GeorgeHahn/Avalon/cgminer/cgminer.c

/*
 * Copyright 2011-2013 Con Kolivas
 * Copyright 2011-2012 Luke Dashjr
 * Copyright 2010 Jeff Garzik
 *
 * This program is free software; you can redistribute it and/or modify it
 * under the terms of the GNU General Public License as published by the Free
 * Software Foundation; either version 3 of the License, or (at your option)
 * any later version.  See COPYING for more details.
 */

#include "config.h"

#ifdef HAVE_CURSES
#include <curses.h>
#endif

#include <stdio.h>
#include <stdlib.h>
#include <string.h>
#include <stdbool.h>
#include <stdint.h>
#include <unistd.h>
#include <sys/time.h>
#include <time.h>
#include <math.h>
#include <stdarg.h>
#include <assert.h>
#include <signal.h>

#ifdef USE_USBUTILS
#include <semaphore.h>
#endif

#include <sys/stat.h>
#include <sys/types.h>

#ifndef WIN32
#include <sys/resource.h>
#endif
#include <ccan/opt/opt.h>
#include <jansson.h>
#include <curl/curl.h>
#include <libgen.h>
#include <sha2.h>

#include "compat.h"
#include "miner.h"
#include "findnonce.h"
#include "adl.h"
#include "driver-opencl.h"
#include "bench_block.h"
#include "scrypt.h"

#ifdef USE_AVALON
#include "driver-avalon.h"
#endif

#if defined(unix) || defined(__APPLE__)
	#include <errno.h>
	#include <fcntl.h>
	#include <sys/wait.h>
#endif

#if defined(USE_BITFORCE) || defined(USE_ICARUS) || defined(USE_AVALON) || defined(USE_MODMINER)
#	define USE_FPGA
#elif defined(USE_ZTEX)
#	define USE_FPGA
#endif

struct strategies strategies[] = {
	{ "Failover" },
	{ "Round Robin" },
	{ "Rotate" },
	{ "Load Balance" },
	{ "Balance" },
};

static char packagename[256];

bool opt_protocol;
static bool opt_benchmark;
bool have_longpoll;
bool want_per_device_stats;
bool use_syslog;
bool opt_quiet;
bool opt_realquiet;
bool opt_loginput;
bool opt_compact;
const int opt_cutofftemp = 95;
int opt_log_interval = 5;
int opt_queue = 1;
int opt_scantime = -1;
int opt_expiry = 120;
static const bool opt_time = true;
unsigned long long global_hashrate;

#if defined(HAVE_OPENCL) || defined(USE_USBUTILS)
int nDevs;
#endif
#ifdef HAVE_OPENCL
int opt_dynamic_interval = 7;
int opt_g_threads = -1;
int gpu_threads;
#ifdef USE_SCRYPT
bool opt_scrypt;
#endif
#endif
bool opt_restart = true;
static bool opt_nogpu;

struct list_head scan_devices;
static bool devices_enabled[MAX_DEVICES];
static int opt_devs_enabled;
static bool opt_display_devs;
static bool opt_removedisabled;
int total_devices;
int zombie_devs;
static int most_devices;
struct cgpu_info **devices;
bool have_opencl;
int mining_threads;
int num_processors;
#ifdef HAVE_CURSES
bool use_curses = true;
#else
bool use_curses;
#endif
static bool opt_submit_stale = true;
static int opt_shares;
bool opt_fail_only;
static bool opt_fix_protocol;
static bool opt_lowmem;
bool opt_autofan;
bool opt_autoengine;
bool opt_noadl;
char *opt_api_allow = NULL;
char *opt_api_groups;
char *opt_api_description = PACKAGE_STRING;
int opt_api_port = 4028;
bool opt_api_listen;
bool opt_api_network;
bool opt_delaynet;
bool opt_disable_pool;
char *opt_icarus_options = NULL;
char *opt_icarus_timing = NULL;
char *opt_klondike_options = NULL;
bool opt_worktime;
#ifdef USE_AVALON
char *opt_avalon_options = NULL;
#endif
#ifdef USE_USBUTILS
char *opt_usb_select = NULL;
int opt_usbdump = -1;
bool opt_usb_list_all;
cgsem_t usb_resource_sem;
#endif

char *opt_kernel_path;
char *cgminer_path;

#if defined(USE_BITFORCE)
bool opt_bfl_noncerange;
#endif
#define QUIET	(opt_quiet || opt_realquiet)

struct thr_info *control_thr;
struct thr_info **mining_thr;
static int gwsched_thr_id;
static int stage_thr_id;
static int watchpool_thr_id;
static int watchdog_thr_id;
#ifdef HAVE_CURSES
static int input_thr_id;
#endif
int gpur_thr_id;
static int api_thr_id;
#ifdef USE_USBUTILS
static int usbres_thr_id;
static int hotplug_thr_id;
#endif
static int total_control_threads;
bool hotplug_mode;
static int new_devices;
static int new_threads;
int hotplug_time = 5;

#ifdef USE_USBUTILS
pthread_mutex_t cgusb_lock;
pthread_mutex_t cgusbres_lock;
cglock_t cgusb_fd_lock;
#endif

pthread_mutex_t hash_lock;
static pthread_mutex_t *stgd_lock;
pthread_mutex_t console_lock;
cglock_t ch_lock;
static pthread_rwlock_t blk_lock;
static pthread_mutex_t sshare_lock;

pthread_rwlock_t netacc_lock;
pthread_rwlock_t mining_thr_lock;
pthread_rwlock_t devices_lock;

static pthread_mutex_t lp_lock;
static pthread_cond_t lp_cond;

pthread_mutex_t restart_lock;
pthread_cond_t restart_cond;

pthread_cond_t gws_cond;

double total_mhashes_done;
static struct timeval total_tv_start, total_tv_end;

cglock_t control_lock;
pthread_mutex_t stats_lock;

int hw_errors;
int total_accepted, total_rejected, total_diff1;
int total_getworks, total_stale, total_discarded;
double total_diff_accepted, total_diff_rejected, total_diff_stale;
static int staged_rollable;
unsigned int new_blocks;
static unsigned int work_block;
unsigned int found_blocks;

unsigned int local_work;
unsigned int total_go, total_ro;

struct pool **pools;
static struct pool *currentpool = NULL;

int total_pools, enabled_pools;
enum pool_strategy pool_strategy = POOL_FAILOVER;
int opt_rotate_period;
static int total_urls, total_users, total_passes, total_userpasses;

static
#ifndef HAVE_CURSES
const
#endif
bool curses_active;

static char current_block[40];

/* Protected by ch_lock */
static char *current_hash;
char *current_fullhash;

static char datestamp[40];
static char blocktime[32];
struct timeval block_timeval;
static char best_share[8] = "0";
double current_diff = 0xFFFFFFFFFFFFFFFFULL;
static char block_diff[8];
uint64_t best_diff = 0;

struct block {
	char hash[40];
	UT_hash_handle hh;
	int block_no;
};

static struct block *blocks = NULL;


int swork_id;

/* For creating a hash database of stratum shares submitted that have not had
 * a response yet */
struct stratum_share {
	UT_hash_handle hh;
	bool block;
	struct work *work;
	int id;
	time_t sshare_time;
};

static struct stratum_share *stratum_shares = NULL;

char *opt_socks_proxy = NULL;

static const char def_conf[] = "cgminer.conf";
static char *default_config;
static bool config_loaded;
static int include_count;
#define JSON_INCLUDE_CONF "include"
#define JSON_LOAD_ERROR "JSON decode of file '%s' failed\n %s"
#define JSON_LOAD_ERROR_LEN strlen(JSON_LOAD_ERROR)
#define JSON_MAX_DEPTH 10
#define JSON_MAX_DEPTH_ERR "Too many levels of JSON includes (limit 10) or a loop"

#if defined(unix) || defined(__APPLE__)
	static char *opt_stderr_cmd = NULL;
	static int forkpid;
#endif // defined(unix)

struct sigaction termhandler, inthandler;

struct thread_q *getq;

static int total_work;
struct work *staged_work = NULL;

struct schedtime {
	bool enable;
	struct tm tm;
};

struct schedtime schedstart;
struct schedtime schedstop;
bool sched_paused;

static bool time_before(struct tm *tm1, struct tm *tm2)
{
	if (tm1->tm_hour < tm2->tm_hour)
		return true;
	if (tm1->tm_hour == tm2->tm_hour && tm1->tm_min < tm2->tm_min)
		return true;
	return false;
}

static bool should_run(void)
{
	struct timeval tv;
	struct tm *tm;

	if (!schedstart.enable && !schedstop.enable)
		return true;

	cgtime(&tv);
	const time_t tmp_time = tv.tv_sec;
	tm = localtime(&tmp_time);
	if (schedstart.enable) {
		if (!schedstop.enable) {
			if (time_before(tm, &schedstart.tm))
				return false;

			/* This is a once off event with no stop time set */
			schedstart.enable = false;
			return true;
		}
		if (time_before(&schedstart.tm, &schedstop.tm)) {
			if (time_before(tm, &schedstop.tm) && !time_before(tm, &schedstart.tm))
				return true;
			return false;
		} /* Times are reversed */
		if (time_before(tm, &schedstart.tm)) {
			if (time_before(tm, &schedstop.tm))
				return true;
			return false;
		}
		return true;
	}
	/* only schedstop.enable == true */
	if (!time_before(tm, &schedstop.tm))
		return false;
	return true;
}

void get_datestamp(char *f, struct timeval *tv)
{
	struct tm *tm;

	const time_t tmp_time = tv->tv_sec;
	tm = localtime(&tmp_time);
	sprintf(f, "[%d-%02d-%02d %02d:%02d:%02d]",
		tm->tm_year + 1900,
		tm->tm_mon + 1,
		tm->tm_mday,
		tm->tm_hour,
		tm->tm_min,
		tm->tm_sec);
}

void get_timestamp(char *f, struct timeval *tv)
{
	struct tm *tm;

	const time_t tmp_time = tv->tv_sec;
	tm = localtime(&tmp_time);
	sprintf(f, "[%02d:%02d:%02d]",
		tm->tm_hour,
		tm->tm_min,
		tm->tm_sec);
}

static char exit_buf[512];

static void applog_and_exit(const char *fmt, ...)
{
	va_list ap;

	va_start(ap, fmt);
	vsnprintf(exit_buf, sizeof(exit_buf), fmt, ap);
	va_end(ap);
	_applog(LOG_ERR, exit_buf);
	exit(1);
}

static pthread_mutex_t sharelog_lock;
static FILE *sharelog_file = NULL;

struct thr_info *get_thread(int thr_id)
{
	struct thr_info *thr;

	rd_lock(&mining_thr_lock);
	thr = mining_thr[thr_id];
	rd_unlock(&mining_thr_lock);

	return thr;
}

static struct cgpu_info *get_thr_cgpu(int thr_id)
{
	struct thr_info *thr = get_thread(thr_id);

	return thr->cgpu;
}

struct cgpu_info *get_devices(int id)
{
	struct cgpu_info *cgpu;

	rd_lock(&devices_lock);
	cgpu = devices[id];
	rd_unlock(&devices_lock);

	return cgpu;
}

static void sharelog(const char*disposition, const struct work*work)
{
	char *target, *hash, *data;
	struct cgpu_info *cgpu;
	unsigned long int t;
	struct pool *pool;
	int thr_id, rv;
	char s[1024];
	size_t ret;

	if (!sharelog_file)
		return;

	thr_id = work->thr_id;
	cgpu = get_thr_cgpu(thr_id);
	pool = work->pool;
	t = (unsigned long int)(work->tv_work_found.tv_sec);
	target = bin2hex(work->target, sizeof(work->target));
	hash = bin2hex(work->hash, sizeof(work->hash));
	data = bin2hex(work->data, sizeof(work->data));

	// timestamp,disposition,target,pool,dev,thr,sharehash,sharedata
	rv = snprintf(s, sizeof(s), "%lu,%s,%s,%s,%s%u,%u,%s,%s\n", t, disposition, target, pool->rpc_url, cgpu->drv->name, cgpu->device_id, thr_id, hash, data);
	free(target);
	free(hash);
	free(data);
	if (rv >= (int)(sizeof(s)))
		s[sizeof(s) - 1] = '\0';
	else if (rv < 0) {
		applog(LOG_ERR, "sharelog printf error");
		return;
	}

	mutex_lock(&sharelog_lock);
	ret = fwrite(s, rv, 1, sharelog_file);
	fflush(sharelog_file);
	mutex_unlock(&sharelog_lock);

	if (ret != 1)
		applog(LOG_ERR, "sharelog fwrite error");
}

static char *getwork_req = "{\"method\": \"getwork\", \"params\": [], \"id\":0}\n";

static char *gbt_req = "{\"id\": 0, \"method\": \"getblocktemplate\", \"params\": [{\"capabilities\": [\"coinbasetxn\", \"workid\", \"coinbase/append\"]}]}\n";

/* Return value is ignored if not called from add_pool_details */
struct pool *add_pool(void)
{
	struct pool *pool;

	pool = calloc(sizeof(struct pool), 1);
	if (!pool)
		quit(1, "Failed to malloc pool in add_pool");
	pool->pool_no = pool->prio = total_pools;
	pools = realloc(pools, sizeof(struct pool *) * (total_pools + 2));
	pools[total_pools++] = pool;
	mutex_init(&pool->pool_lock);
	if (unlikely(pthread_cond_init(&pool->cr_cond, NULL)))
		quit(1, "Failed to pthread_cond_init in add_pool");
	cglock_init(&pool->data_lock);
	mutex_init(&pool->stratum_lock);
	cglock_init(&pool->gbt_lock);
	INIT_LIST_HEAD(&pool->curlring);

	/* Make sure the pool doesn't think we've been idle since time 0 */
	pool->tv_idle.tv_sec = ~0UL;

	pool->rpc_req = getwork_req;
	pool->rpc_proxy = NULL;

	return pool;
}

/* Pool variant of test and set */
static bool pool_tset(struct pool *pool, bool *var)
{
	bool ret;

	mutex_lock(&pool->pool_lock);
	ret = *var;
	*var = true;
	mutex_unlock(&pool->pool_lock);

	return ret;
}

bool pool_tclear(struct pool *pool, bool *var)
{
	bool ret;

	mutex_lock(&pool->pool_lock);
	ret = *var;
	*var = false;
	mutex_unlock(&pool->pool_lock);

	return ret;
}

struct pool *current_pool(void)
{
	struct pool *pool;

	cg_rlock(&control_lock);
	pool = currentpool;
	cg_runlock(&control_lock);

	return pool;
}

char *set_int_range(const char *arg, int *i, int min, int max)
{
	char *err = opt_set_intval(arg, i);

	if (err)
		return err;

	if (*i < min || *i > max)
		return "Value out of range";

	return NULL;
}

static char *set_int_0_to_9999(const char *arg, int *i)
{
	return set_int_range(arg, i, 0, 9999);
}

static char *set_int_1_to_65535(const char *arg, int *i)
{
	return set_int_range(arg, i, 1, 65535);
}

static char *set_int_0_to_10(const char *arg, int *i)
{
	return set_int_range(arg, i, 0, 10);
}

#ifdef USE_AVALON
static char *set_int_0_to_100(const char *arg, int *i)
{
	return set_int_range(arg, i, 0, 100);
}
#endif

static char *set_int_1_to_10(const char *arg, int *i)
{
	return set_int_range(arg, i, 1, 10);
}

#ifdef USE_FPGA_SERIAL
static char *add_serial(char *arg)
{
	string_elist_add(arg, &scan_devices);
	return NULL;
}
#endif

void get_intrange(char *arg, int *val1, int *val2)
{
	if (sscanf(arg, "%d-%d", val1, val2) == 1)
		*val2 = *val1;
}

static char *set_devices(char *arg)
{
	int i, val1 = 0, val2 = 0;
	char *nextptr;

	if (*arg) {
		if (*arg == '?') {
			opt_display_devs = true;
			return NULL;
		}
	} else
		return "Invalid device parameters";

	nextptr = strtok(arg, ",");
	if (nextptr == NULL)
		return "Invalid parameters for set devices";
	get_intrange(nextptr, &val1, &val2);
	if (val1 < 0 || val1 > MAX_DEVICES || val2 < 0 || val2 > MAX_DEVICES ||
	    val1 > val2) {
		return "Invalid value passed to set devices";
	}

	for (i = val1; i <= val2; i++) {
		devices_enabled[i] = true;
		opt_devs_enabled++;
	}

	while ((nextptr = strtok(NULL, ",")) != NULL) {
		get_intrange(nextptr, &val1, &val2);
		if (val1 < 0 || val1 > MAX_DEVICES || val2 < 0 || val2 > MAX_DEVICES ||
		val1 > val2) {
			return "Invalid value passed to set devices";
		}

		for (i = val1; i <= val2; i++) {
			devices_enabled[i] = true;
			opt_devs_enabled++;
		}
	}

	return NULL;
}

static char *set_balance(enum pool_strategy *strategy)
{
	*strategy = POOL_BALANCE;
	return NULL;
}

static char *set_loadbalance(enum pool_strategy *strategy)
{
	*strategy = POOL_LOADBALANCE;
	return NULL;
}

static char *set_rotate(const char *arg, int *i)
{
	pool_strategy = POOL_ROTATE;
	return set_int_range(arg, i, 0, 9999);
}

static char *set_rr(enum pool_strategy *strategy)
{
	*strategy = POOL_ROUNDROBIN;
	return NULL;
}

/* Detect that url is for a stratum protocol either via the presence of
 * stratum+tcp or by detecting a stratum server response */
bool detect_stratum(struct pool *pool, char *url)
{
	if (!extract_sockaddr(pool, url))
		return false;

	if (!strncasecmp(url, "stratum+tcp://", 14)) {
		pool->rpc_url = strdup(url);
		pool->has_stratum = true;
		pool->stratum_url = pool->sockaddr_url;
		return true;
	}

	return false;
}

static char *set_url(char *arg)
{
	struct pool *pool;

	total_urls++;
	if (total_urls > total_pools)
		add_pool();
	pool = pools[total_urls - 1];

	arg = get_proxy(arg, pool);

	if (detect_stratum(pool, arg))
		return NULL;

	opt_set_charp(arg, &pool->rpc_url);
	if (strncmp(arg, "http://", 7) &&
	    strncmp(arg, "https://", 8)) {
		char *httpinput;

		httpinput = malloc(255);
		if (!httpinput)
			quit(1, "Failed to malloc httpinput");
		strcpy(httpinput, "http://");
		strncat(httpinput, arg, 248);
		pool->rpc_url = httpinput;
	}

	return NULL;
}

static char *set_user(const char *arg)
{
	struct pool *pool;

	if (total_userpasses)
		return "Use only user + pass or userpass, but not both";
	total_users++;
	if (total_users > total_pools)
		add_pool();

	pool = pools[total_users - 1];
	opt_set_charp(arg, &pool->rpc_user);

	return NULL;
}

static char *set_pass(const char *arg)
{
	struct pool *pool;

	if (total_userpasses)
		return "Use only user + pass or userpass, but not both";
	total_passes++;
	if (total_passes > total_pools)
		add_pool();

	pool = pools[total_passes - 1];
	opt_set_charp(arg, &pool->rpc_pass);

	return NULL;
}

static char *set_userpass(const char *arg)
{
	struct pool *pool;
	char *updup;

	if (total_users || total_passes)
		return "Use only user + pass or userpass, but not both";
	total_userpasses++;
	if (total_userpasses > total_pools)
		add_pool();

	pool = pools[total_userpasses - 1];
	updup = strdup(arg);
	opt_set_charp(arg, &pool->rpc_userpass);
	pool->rpc_user = strtok(updup, ":");
	if (!pool->rpc_user)
		return "Failed to find : delimited user info";
	pool->rpc_pass = strtok(NULL, ":");
	if (!pool->rpc_pass)
		return "Failed to find : delimited pass info";

	return NULL;
}

static char *enable_debug(bool *flag)
{
	*flag = true;
	/* Turn on verbose output, too. */
	opt_log_output = true;
	return NULL;
}

static char *set_schedtime(const char *arg, struct schedtime *st)
{
	if (sscanf(arg, "%d:%d", &st->tm.tm_hour, &st->tm.tm_min) != 2)
		return "Invalid time set, should be HH:MM";
	if (st->tm.tm_hour > 23 || st->tm.tm_min > 59 || st->tm.tm_hour < 0 || st->tm.tm_min < 0)
		return "Invalid time set.";
	st->enable = true;
	return NULL;
}

static char* set_sharelog(char *arg)
{
	char *r = "";
	long int i = strtol(arg, &r, 10);

	if ((!*r) && i >= 0 && i <= INT_MAX) {
		sharelog_file = fdopen((int)i, "a");
		if (!sharelog_file)
			applog(LOG_ERR, "Failed to open fd %u for share log", (unsigned int)i);
	} else if (!strcmp(arg, "-")) {
		sharelog_file = stdout;
		if (!sharelog_file)
			applog(LOG_ERR, "Standard output missing for share log");
	} else {
		sharelog_file = fopen(arg, "a");
		if (!sharelog_file)
			applog(LOG_ERR, "Failed to open %s for share log", arg);
	}

	return NULL;
}

static char *temp_cutoff_str = NULL;

char *set_temp_cutoff(char *arg)
{
	int val;

	if (!(arg && arg[0]))
		return "Invalid parameters for set temp cutoff";
	val = atoi(arg);
	if (val < 0 || val > 200)
		return "Invalid value passed to set temp cutoff";
	temp_cutoff_str = arg;

	return NULL;
}

static void load_temp_cutoffs()
{
	int i, val = 0, device = 0;
	char *nextptr;

	if (temp_cutoff_str) {
		for (device = 0, nextptr = strtok(temp_cutoff_str, ","); nextptr; ++device, nextptr = strtok(NULL, ",")) {
			if (device >= total_devices)
				quit(1, "Too many values passed to set temp cutoff");
			val = atoi(nextptr);
			if (val < 0 || val > 200)
				quit(1, "Invalid value passed to set temp cutoff");

			rd_lock(&devices_lock);
			devices[device]->cutofftemp = val;
			rd_unlock(&devices_lock);
		}
	} else {
		rd_lock(&devices_lock);
		for (i = device; i < total_devices; ++i) {
			if (!devices[i]->cutofftemp)
				devices[i]->cutofftemp = opt_cutofftemp;
		}
		rd_unlock(&devices_lock);

		return;
	}
	if (device <= 1) {
		rd_lock(&devices_lock);
		for (i = device; i < total_devices; ++i)
			devices[i]->cutofftemp = val;
		rd_unlock(&devices_lock);
	}
}

static char *set_api_allow(const char *arg)
{
	opt_set_charp(arg, &opt_api_allow);

	return NULL;
}

static char *set_api_groups(const char *arg)
{
	opt_set_charp(arg, &opt_api_groups);

	return NULL;
}

static char *set_api_description(const char *arg)
{
	opt_set_charp(arg, &opt_api_description);

	return NULL;
}

#ifdef USE_ICARUS
static char *set_icarus_options(const char *arg)
{
	opt_set_charp(arg, &opt_icarus_options);

	return NULL;
}

static char *set_icarus_timing(const char *arg)
{
	opt_set_charp(arg, &opt_icarus_timing);

	return NULL;
}
#endif

#ifdef USE_KLONDIKE
static char *set_klondike_options(const char *arg)
{
	opt_set_charp(arg, &opt_klondike_options);

	return NULL;
}
#endif

#ifdef USE_AVALON
static char *set_avalon_options(const char *arg)
{
	opt_set_charp(arg, &opt_avalon_options);

	return NULL;
}
#endif

#ifdef USE_USBUTILS
static char *set_usb_select(const char *arg)
{
	opt_set_charp(arg, &opt_usb_select);

	return NULL;
}
#endif

static char *set_null(const char __maybe_unused *arg)
{
	return NULL;
}

/* These options are available from config file or commandline */
static struct opt_table opt_config_table[] = {
	OPT_WITH_ARG("--api-allow",
		     set_api_allow, NULL, NULL,
		     "Allow API access only to the given list of [G:]IP[/Prefix] addresses[/subnets]"),
	OPT_WITH_ARG("--api-description",
		     set_api_description, NULL, NULL,
		     "Description placed in the API status header, default: cgminer version"),
	OPT_WITH_ARG("--api-groups",
		     set_api_groups, NULL, NULL,
		     "API one letter groups G:cmd:cmd[,P:cmd:*...] defining the cmds a groups can use"),
	OPT_WITHOUT_ARG("--api-listen",
			opt_set_bool, &opt_api_listen,
			"Enable API, default: disabled"),
	OPT_WITHOUT_ARG("--api-network",
			opt_set_bool, &opt_api_network,
			"Allow API (if enabled) to listen on/for any address, default: only 127.0.0.1"),
	OPT_WITH_ARG("--api-port",
		     set_int_1_to_65535, opt_show_intval, &opt_api_port,
		     "Port number of miner API"),
#ifdef HAVE_ADL
	OPT_WITHOUT_ARG("--auto-fan",
			opt_set_bool, &opt_autofan,
			"Automatically adjust all GPU fan speeds to maintain a target temperature"),
	OPT_WITHOUT_ARG("--auto-gpu",
			opt_set_bool, &opt_autoengine,
			"Automatically adjust all GPU engine clock speeds to maintain a target temperature"),
#endif
	OPT_WITHOUT_ARG("--balance",
		     set_balance, &pool_strategy,
		     "Change multipool strategy from failover to even share balance"),
	OPT_WITHOUT_ARG("--benchmark",
			opt_set_bool, &opt_benchmark,
			"Run cgminer in benchmark mode - produces no shares"),
#if defined(USE_BITFORCE)
	OPT_WITHOUT_ARG("--bfl-range",
			opt_set_bool, &opt_bfl_noncerange,
			"Use nonce range on bitforce devices if supported"),
#endif
#ifdef HAVE_CURSES
	OPT_WITHOUT_ARG("--compact",
			opt_set_bool, &opt_compact,
			"Use compact display without per device statistics"),
#endif
	OPT_WITHOUT_ARG("--debug|-D",
		     enable_debug, &opt_debug,
		     "Enable debug output"),
	OPT_WITH_ARG("--device|-d",
		     set_devices, NULL, NULL,
	             "Select device to use, one value, range and/or comma separated (e.g. 0-2,4) default: all"),
	OPT_WITHOUT_ARG("--disable-gpu|-G",
			opt_set_bool, &opt_nogpu,
#ifdef HAVE_OPENCL
			"Disable GPU mining even if suitable devices exist"
#else
			opt_hidden
#endif
	),
	OPT_WITHOUT_ARG("--disable-rejecting",
			opt_set_bool, &opt_disable_pool,
			"Automatically disable pools that continually reject shares"),
	OPT_WITH_ARG("--expiry|-E",
		     set_int_0_to_9999, opt_show_intval, &opt_expiry,
		     "Upper bound on how many seconds after getting work we consider a share from it stale"),
	OPT_WITHOUT_ARG("--failover-only",
			opt_set_bool, &opt_fail_only,
			"Don't leak work to backup pools when primary pool is lagging"),
	OPT_WITHOUT_ARG("--fix-protocol",
			opt_set_bool, &opt_fix_protocol,
			"Do not redirect to a different getwork protocol (eg. stratum)"),
#ifdef HAVE_OPENCL
	OPT_WITH_ARG("--gpu-dyninterval",
		     set_int_1_to_65535, opt_show_intval, &opt_dynamic_interval,
		     "Set the refresh interval in ms for GPUs using dynamic intensity"),
	OPT_WITH_ARG("--gpu-platform",
		     set_int_0_to_9999, opt_show_intval, &opt_platform_id,
		     "Select OpenCL platform ID to use for GPU mining"),
	OPT_WITH_ARG("--gpu-threads|-g",
		     set_int_1_to_10, opt_show_intval, &opt_g_threads,
		     "Number of threads per GPU (1 - 10)"),
#ifdef HAVE_ADL
	OPT_WITH_ARG("--gpu-engine",
		     set_gpu_engine, NULL, NULL,
		     "GPU engine (over)clock range in Mhz - one value, range and/or comma separated list (e.g. 850-900,900,750-850)"),
	OPT_WITH_ARG("--gpu-fan",
		     set_gpu_fan, NULL, NULL,
		     "GPU fan percentage range - one value, range and/or comma separated list (e.g. 0-85,85,65)"),
	OPT_WITH_ARG("--gpu-map",
		     set_gpu_map, NULL, NULL,
		     "Map OpenCL to ADL device order manually, paired CSV (e.g. 1:0,2:1 maps OpenCL 1 to ADL 0, 2 to 1)"),
	OPT_WITH_ARG("--gpu-memclock",
		     set_gpu_memclock, NULL, NULL,
		     "Set the GPU memory (over)clock in Mhz - one value for all or separate by commas for per card"),
	OPT_WITH_ARG("--gpu-memdiff",
		     set_gpu_memdiff, NULL, NULL,
		     "Set a fixed difference in clock speed between the GPU and memory in auto-gpu mode"),
	OPT_WITH_ARG("--gpu-powertune",
		     set_gpu_powertune, NULL, NULL,
		     "Set the GPU powertune percentage - one value for all or separate by commas for per card"),
	OPT_WITHOUT_ARG("--gpu-reorder",
			opt_set_bool, &opt_reorder,
			"Attempt to reorder GPU devices according to PCI Bus ID"),
	OPT_WITH_ARG("--gpu-vddc",
		     set_gpu_vddc, NULL, NULL,
		     "Set the GPU voltage in Volts - one value for all or separate by commas for per card"),
#endif
#ifdef USE_SCRYPT
	OPT_WITH_ARG("--lookup-gap",
		     set_lookup_gap, NULL, NULL,
		     "Set GPU lookup gap for scrypt mining, comma separated"),
#endif
	OPT_WITH_ARG("--intensity|-I",
		     set_intensity, NULL, NULL,
		     "Intensity of GPU scanning (d or " _MIN_INTENSITY_STR " -> " _MAX_INTENSITY_STR ", default: d to maintain desktop interactivity)"),
#endif
	OPT_WITH_ARG("--hotplug",
		     set_int_0_to_9999, NULL, &hotplug_time,
#ifdef USE_USBUTILS
		     "Seconds between hotplug checks (0 means never check)"
#else
		     opt_hidden
#endif
		    ),
#if defined(HAVE_OPENCL) || defined(HAVE_MODMINER)
	OPT_WITH_ARG("--kernel-path|-K",
		     opt_set_charp, opt_show_charp, &opt_kernel_path,
	             "Specify a path to where bitstream and kernel files are"),
#endif
#ifdef HAVE_OPENCL
	OPT_WITH_ARG("--kernel|-k",
		     set_kernel, NULL, NULL,
		     "Override sha256 kernel to use (diablo, poclbm, phatk or diakgcn) - one value or comma separated"),
#endif
#ifdef USE_ICARUS
	OPT_WITH_ARG("--icarus-options",
		     set_icarus_options, NULL, NULL,
		     opt_hidden),
	OPT_WITH_ARG("--icarus-timing",
		     set_icarus_timing, NULL, NULL,
		     opt_hidden),
#endif
#ifdef USE_KLONDIKE
	OPT_WITH_ARG("--klondike-options",
		     set_klondike_options, NULL, NULL,
		     opt_hidden),
#endif
#ifdef USE_AVALON
	OPT_WITHOUT_ARG("--avalon-auto",
			opt_set_bool, &opt_avalon_auto,
			"Adjust avalon overclock frequency dynamically for best hashrate"),
	OPT_WITH_ARG("--avalon-cutoff",
		     set_int_0_to_100, opt_show_intval, &opt_avalon_overheat,
		     "Set avalon overheat cut off temperature"),
	OPT_WITH_ARG("--avalon-fan",
		     set_avalon_fan, NULL, NULL,
		     "Set fanspeed percentage for avalon, single value or range (default: 20-100)"),
	OPT_WITH_ARG("--avalon-freq",
		     set_avalon_freq, NULL, NULL,
		     "Set frequency range for avalon-auto, single value or range"),
	OPT_WITH_ARG("--avalon-options",
		     set_avalon_options, NULL, NULL,
		     "Set avalon options baud:miners:asic:timeout:freq"),
	OPT_WITH_ARG("--avalon-temp",
		     set_int_0_to_100, opt_show_intval, &opt_avalon_temp,
		     "Set avalon target temperature"),
#endif
	OPT_WITHOUT_ARG("--load-balance",
		     set_loadbalance, &pool_strategy,
		     "Change multipool strategy from failover to efficiency based balance"),
	OPT_WITH_ARG("--log|-l",
		     set_int_0_to_9999, opt_show_intval, &opt_log_interval,
		     "Interval in seconds between log output"),
	OPT_WITHOUT_ARG("--lowmem",
			opt_set_bool, &opt_lowmem,
			"Minimise caching of shares for low memory applications"),
#if defined(unix) || defined(__APPLE__)
	OPT_WITH_ARG("--monitor|-m",
		     opt_set_charp, NULL, &opt_stderr_cmd,
		     "Use custom pipe cmd for output messages"),
#endif // defined(unix)
	OPT_WITHOUT_ARG("--net-delay",
			opt_set_bool, &opt_delaynet,
			"Impose small delays in networking to not overload slow routers"),
	OPT_WITHOUT_ARG("--no-adl",
			opt_set_bool, &opt_noadl,
#ifdef HAVE_ADL
			"Disable the ATI display library used for monitoring and setting GPU parameters"
#else
			opt_hidden
#endif
			),
	OPT_WITHOUT_ARG("--no-pool-disable",
			opt_set_invbool, &opt_disable_pool,
			opt_hidden),
	OPT_WITHOUT_ARG("--no-restart",
			opt_set_invbool, &opt_restart,
#ifdef HAVE_OPENCL
			"Do not attempt to restart GPUs that hang"
#else
			opt_hidden
#endif
	),
	OPT_WITHOUT_ARG("--no-submit-stale",
			opt_set_invbool, &opt_submit_stale,
		        "Don't submit shares if they are detected as stale"),
	OPT_WITH_ARG("--pass|-p",
		     set_pass, NULL, NULL,
		     "Password for bitcoin JSON-RPC server"),
	OPT_WITHOUT_ARG("--per-device-stats",
			opt_set_bool, &want_per_device_stats,
			"Force verbose mode and output per-device statistics"),
	OPT_WITHOUT_ARG("--protocol-dump|-P",
			opt_set_bool, &opt_protocol,
			"Verbose dump of protocol-level activities"),
	OPT_WITH_ARG("--queue|-Q",
		     set_int_0_to_9999, opt_show_intval, &opt_queue,
		     "Minimum number of work items to have queued (0+)"),
	OPT_WITHOUT_ARG("--quiet|-q",
			opt_set_bool, &opt_quiet,
			"Disable logging output, display status and errors"),
	OPT_WITHOUT_ARG("--real-quiet",
			opt_set_bool, &opt_realquiet,
			"Disable all output"),
	OPT_WITHOUT_ARG("--remove-disabled",
		     opt_set_bool, &opt_removedisabled,
	         "Remove disabled devices entirely, as if they didn't exist"),
	OPT_WITH_ARG("--retries",
		     set_null, NULL, NULL,
		     opt_hidden),
	OPT_WITH_ARG("--retry-pause",
		     set_null, NULL, NULL,
		     opt_hidden),
	OPT_WITH_ARG("--rotate",
		     set_rotate, opt_show_intval, &opt_rotate_period,
		     "Change multipool strategy from failover to regularly rotate at N minutes"),
	OPT_WITHOUT_ARG("--round-robin",
		     set_rr, &pool_strategy,
		     "Change multipool strategy from failover to round robin on failure"),
#ifdef USE_FPGA_SERIAL
	OPT_WITH_ARG("--scan-serial|-S",
		     add_serial, NULL, NULL,
		     "Serial port to probe for Serial FPGA Mining device"),
#endif
	OPT_WITH_ARG("--scan-time|-s",
		     set_int_0_to_9999, opt_show_intval, &opt_scantime,
		     "Upper bound on time spent scanning current work, in seconds"),
	OPT_WITH_ARG("--sched-start",
		     set_schedtime, NULL, &schedstart,
		     "Set a time of day in HH:MM to start mining (a once off without a stop time)"),
	OPT_WITH_ARG("--sched-stop",
		     set_schedtime, NULL, &schedstop,
		     "Set a time of day in HH:MM to stop mining (will quit without a start time)"),
#ifdef USE_SCRYPT
	OPT_WITHOUT_ARG("--scrypt",
			opt_set_bool, &opt_scrypt,
			"Use the scrypt algorithm for mining (litecoin only)"),
	OPT_WITH_ARG("--shaders",
		     set_shaders, NULL, NULL,
		     "GPU shaders per card for tuning scrypt, comma separated"),
#endif
	OPT_WITH_ARG("--sharelog",
		     set_sharelog, NULL, NULL,
		     "Append share log to file"),
	OPT_WITH_ARG("--shares",
		     opt_set_intval, NULL, &opt_shares,
		     "Quit after mining N shares (default: unlimited)"),
	OPT_WITH_ARG("--socks-proxy",
		     opt_set_charp, NULL, &opt_socks_proxy,
		     "Set socks4 proxy (host:port)"),
#ifdef HAVE_SYSLOG_H
	OPT_WITHOUT_ARG("--syslog",
			opt_set_bool, &use_syslog,
			"Use system log for output messages (default: standard error)"),
#endif
#if defined(HAVE_ADL) || defined(USE_BITFORCE) || defined(USE_MODMINER) || defined(USE_BFLSC)
	OPT_WITH_ARG("--temp-cutoff",
		     set_temp_cutoff, opt_show_intval, &opt_cutofftemp,
		     "Temperature where a device will be automatically disabled, one value or comma separated list"),
#endif
#ifdef HAVE_ADL
	OPT_WITH_ARG("--temp-hysteresis",
		     set_int_1_to_10, opt_show_intval, &opt_hysteresis,
		     "Set how much the temperature can fluctuate outside limits when automanaging speeds"),
	OPT_WITH_ARG("--temp-overheat",
		     set_temp_overheat, opt_show_intval, &opt_overheattemp,
		     "Overheat temperature when automatically managing fan and GPU speeds, one value or comma separated list"),
	OPT_WITH_ARG("--temp-target",
		     set_temp_target, opt_show_intval, &opt_targettemp,
		     "Target temperature when automatically managing fan and GPU speeds, one value or comma separated list"),
#endif
	OPT_WITHOUT_ARG("--text-only|-T",
			opt_set_invbool, &use_curses,
#ifdef HAVE_CURSES
			"Disable ncurses formatted screen output"
#else
			opt_hidden
#endif
	),
#ifdef USE_SCRYPT
	OPT_WITH_ARG("--thread-concurrency",
		     set_thread_concurrency, NULL, NULL,
		     "Set GPU thread concurrency for scrypt mining, comma separated"),
#endif
	OPT_WITH_ARG("--url|-o",
		     set_url, NULL, NULL,
		     "URL for bitcoin JSON-RPC server"),
	OPT_WITH_ARG("--user|-u",
		     set_user, NULL, NULL,
		     "Username for bitcoin JSON-RPC server"),
#ifdef USE_USBUTILS
	OPT_WITH_ARG("--usb",
		     set_usb_select, NULL, NULL,
		     "USB device selection"),
	OPT_WITH_ARG("--usb-dump",
		     set_int_0_to_10, opt_show_intval, &opt_usbdump,
		     opt_hidden),
	OPT_WITHOUT_ARG("--usb-list-all",
			opt_set_bool, &opt_usb_list_all,
			opt_hidden),
#endif
#ifdef HAVE_OPENCL
	OPT_WITH_ARG("--vectors|-v",
		     set_vector, NULL, NULL,
		     "Override detected optimal vector (1, 2 or 4) - one value or comma separated list"),
#endif
	OPT_WITHOUT_ARG("--verbose",
			opt_set_bool, &opt_log_output,
			"Log verbose output to stderr as well as status output"),
#ifdef HAVE_OPENCL
	OPT_WITH_ARG("--worksize|-w",
		     set_worksize, NULL, NULL,
		     "Override detected optimal worksize - one value or comma separated list"),
#endif
	OPT_WITH_ARG("--userpass|-O",
		     set_userpass, NULL, NULL,
		     "Username:Password pair for bitcoin JSON-RPC server"),
	OPT_WITHOUT_ARG("--worktime",
			opt_set_bool, &opt_worktime,
			"Display extra work time debug information"),
	OPT_WITH_ARG("--pools",
			opt_set_bool, NULL, NULL, opt_hidden),
	OPT_ENDTABLE
};

static char *load_config(const char *arg, void __maybe_unused *unused);

static int fileconf_load;

static char *parse_config(json_t *config, bool fileconf)
{
	static char err_buf[200];
	struct opt_table *opt;
	json_t *val;

	if (fileconf && !fileconf_load)
		fileconf_load = 1;

	for (opt = opt_config_table; opt->type != OPT_END; opt++) {
		char *p, *name;

		/* We don't handle subtables. */
		assert(!(opt->type & OPT_SUBTABLE));

		/* Pull apart the option name(s). */
		name = strdup(opt->names);
		for (p = strtok(name, "|"); p; p = strtok(NULL, "|")) {
			char *err = NULL;

			/* Ignore short options. */
			if (p[1] != '-')
				continue;

			val = json_object_get(config, p+2);
			if (!val)
				continue;

			if ((opt->type & OPT_HASARG) && json_is_string(val)) {
				err = opt->cb_arg(json_string_value(val),
						  opt->u.arg);
			} else if ((opt->type & OPT_HASARG) && json_is_array(val)) {
				int n, size = json_array_size(val);

				for (n = 0; n < size && !err; n++) {
					if (json_is_string(json_array_get(val, n)))
						err = opt->cb_arg(json_string_value(json_array_get(val, n)), opt->u.arg);
					else if (json_is_object(json_array_get(val, n)))
						err = parse_config(json_array_get(val, n), false);
				}
			} else if ((opt->type & OPT_NOARG) && json_is_true(val))
				err = opt->cb(opt->u.arg);
			else
				err = "Invalid value";

			if (err) {
				/* Allow invalid values to be in configuration
				 * file, just skipping over them provided the
				 * JSON is still valid after that. */
				if (fileconf) {
					applog(LOG_ERR, "Invalid config option %s: %s", p, err);
					fileconf_load = -1;
				} else {
					sprintf(err_buf, "Parsing JSON option %s: %s",
						p, err);
					return err_buf;
				}
			}
		}
		free(name);
	}

	val = json_object_get(config, JSON_INCLUDE_CONF);
	if (val && json_is_string(val))
		return load_config(json_string_value(val), NULL);

	return NULL;
}

char *cnfbuf = NULL;

static char *load_config(const char *arg, void __maybe_unused *unused)
{
	json_error_t err;
	json_t *config;
	char *json_error;

	if (!cnfbuf)
		cnfbuf = strdup(arg);

	if (++include_count > JSON_MAX_DEPTH)
		return JSON_MAX_DEPTH_ERR;

#if JANSSON_MAJOR_VERSION > 1
	config = json_load_file(arg, 0, &err);
#else
	config = json_load_file(arg, &err);
#endif
	if (!json_is_object(config)) {
		json_error = malloc(JSON_LOAD_ERROR_LEN + strlen(arg) + strlen(err.text));
		if (!json_error)
			quit(1, "Malloc failure in json error");

		sprintf(json_error, JSON_LOAD_ERROR, arg, err.text);
		return json_error;
	}

	config_loaded = true;

	/* Parse the config now, so we can override it.  That can keep pointers
	 * so don't free config object. */
	return parse_config(config, true);
}

static char *set_default_config(const char *arg)
{
	opt_set_charp(arg, &default_config);

	return NULL;
}

void default_save_file(char *filename);

static void load_default_config(void)
{
	cnfbuf = malloc(PATH_MAX);

	default_save_file(cnfbuf);

	if (!access(cnfbuf, R_OK))
		load_config(cnfbuf, NULL);
	else {
		free(cnfbuf);
		cnfbuf = NULL;
	}
}

extern const char *opt_argv0;

static char *opt_verusage_and_exit(const char *extra)
{
	printf("%s\nBuilt with "
#ifdef USE_BFLSC
		"bflsc "
#endif
#ifdef USE_BFLSC
		"klondike "
#endif
#ifdef HAVE_OPENCL
		"GPU "
#endif
#ifdef USE_BITFORCE
		"bitforce "
#endif
#ifdef USE_ICARUS
		"icarus "
#endif
#ifdef USE_AVALON
		"avalon "
#endif
#ifdef USE_MODMINER
		"modminer "
#endif
#ifdef USE_ZTEX
		"ztex "
#endif
#ifdef USE_SCRYPT
		"scrypt "
#endif
		"mining support.\n"
		, packagename);
	printf("%s", opt_usage(opt_argv0, extra));
	fflush(stdout);
	exit(0);
}

#if defined(HAVE_OPENCL) || defined(USE_USBUTILS)
char *display_devs(int *ndevs)
{
	*ndevs = 0;
#ifdef HAVE_OPENCL
	print_ndevs(ndevs);
#endif
#ifdef USE_USBUTILS
	usb_all(0);
#endif
	exit(*ndevs);
}
#endif

/* These options are available from commandline only */
static struct opt_table opt_cmdline_table[] = {
	OPT_WITH_ARG("--config|-c",
		     load_config, NULL, NULL,
		     "Load a JSON-format configuration file\n"
		     "See example.conf for an example configuration."),
	OPT_WITH_ARG("--default-config",
		     set_default_config, NULL, NULL,
		     "Specify the filename of the default config file\n"
		     "Loaded at start and used when saving without a name."),
	OPT_WITHOUT_ARG("--help|-h",
			opt_verusage_and_exit, NULL,
			"Print this message"),
#if defined(HAVE_OPENCL) || defined(USE_USBUTILS)
	OPT_WITHOUT_ARG("--ndevs|-n",
			display_devs, &nDevs,
			"Display "
#ifdef HAVE_OPENCL
			"number of detected GPUs, OpenCL platform information, "
#endif
#ifdef USE_USBUTILS
			"all USB devices, "
#endif
			"and exit"),
#endif
	OPT_WITHOUT_ARG("--version|-V",
			opt_version_and_exit, packagename,
			"Display version and exit"),
	OPT_ENDTABLE
};

static bool jobj_binary(const json_t *obj, const char *key,
			void *buf, size_t buflen, bool required)
{
	const char *hexstr;
	json_t *tmp;

	tmp = json_object_get(obj, key);
	if (unlikely(!tmp)) {
		if (unlikely(required))
			applog(LOG_ERR, "JSON key '%s' not found", key);
		return false;
	}
	hexstr = json_string_value(tmp);
	if (unlikely(!hexstr)) {
		applog(LOG_ERR, "JSON key '%s' is not a string", key);
		return false;
	}
	if (!hex2bin(buf, hexstr, buflen))
		return false;

	return true;
}

static void calc_midstate(struct work *work)
{
	unsigned char data[64];
	uint32_t *data32 = (uint32_t *)data;
	sha2_context ctx;

	flip64(data32, work->data);
	sha2_starts(&ctx);
	sha2_update(&ctx, data, 64);
	memcpy(work->midstate, ctx.state, 32);
	endian_flip32(work->midstate, work->midstate);
}

static struct work *make_work(void)
{
	struct work *work = calloc(1, sizeof(struct work));

	if (unlikely(!work))
		quit(1, "Failed to calloc work in make_work");

	cg_wlock(&control_lock);
	work->id = total_work++;
	cg_wunlock(&control_lock);

	return work;
}

/* This is the central place all work that is about to be retired should be
 * cleaned to remove any dynamically allocated arrays within the struct */
void clean_work(struct work *work)
{
	free(work->job_id);
	free(work->nonce2);
	free(work->ntime);
	free(work->gbt_coinbase);
	free(work->nonce1);
	memset(work, 0, sizeof(struct work));
}

/* All dynamically allocated work structs should be freed here to not leak any
 * ram from arrays allocated within the work struct */
void free_work(struct work *work)
{
	clean_work(work);
	free(work);
}

/* Generate a GBT coinbase from the existing GBT variables stored. Must be
 * entered under gbt_lock */
static void __build_gbt_coinbase(struct pool *pool)
{
	unsigned char *coinbase;
	int cbt_len, orig_len;
	uint8_t *extra_len;
	size_t cal_len;

	cbt_len = strlen(pool->coinbasetxn) / 2;
	pool->coinbase_len = cbt_len + 4;
	/* We add 4 bytes of extra data corresponding to nonce2 of stratum */
	cal_len = pool->coinbase_len + 1;
	align_len(&cal_len);
	coinbase = calloc(cal_len, 1);
	hex2bin(coinbase, pool->coinbasetxn, 42);
	extra_len = (uint8_t *)(coinbase + 41);
	orig_len = *extra_len;
	hex2bin(coinbase + 42, pool->coinbasetxn + 84, orig_len);
	memcpy(coinbase + 42 + orig_len, &pool->nonce2, 4);
	*extra_len += 4;
	hex2bin(coinbase + 42 + *extra_len, pool->coinbasetxn + 84 + (orig_len * 2), cbt_len - orig_len - 42);
	pool->nonce2++;
	free(pool->gbt_coinbase);
	pool->gbt_coinbase = coinbase;
}

static void gen_hash(unsigned char *data, unsigned char *hash, int len);

/* Process transactions with GBT by storing the binary value of the first
 * transaction, and the hashes of the remaining transactions since these
 * remain constant with an altered coinbase when generating work. Must be
 * entered under gbt_lock */
static bool __build_gbt_txns(struct pool *pool, json_t *res_val)
{
	json_t *txn_array;
	bool ret = false;
	size_t cal_len;
	int i;

	free(pool->txn_hashes);
	pool->txn_hashes = NULL;
	pool->gbt_txns = 0;

	txn_array = json_object_get(res_val, "transactions");
	if (!json_is_array(txn_array))
		goto out;

	ret = true;
	pool->gbt_txns = json_array_size(txn_array);
	if (!pool->gbt_txns)
		goto out;

	pool->txn_hashes = calloc(32 * (pool->gbt_txns + 1), 1);
	if (unlikely(!pool->txn_hashes))
		quit(1, "Failed to calloc txn_hashes in __build_gbt_txns");

	for (i = 0; i < pool->gbt_txns; i++) {
		json_t *txn_val = json_object_get(json_array_get(txn_array, i), "data");
		const char *txn = json_string_value(txn_val);
		int txn_len = strlen(txn);
		unsigned char *txn_bin;

		cal_len = txn_len;
		align_len(&cal_len);
		txn_bin = calloc(cal_len, 1);
		if (unlikely(!txn_bin))
			quit(1, "Failed to calloc txn_bin in __build_gbt_txns");
		if (unlikely(!hex2bin(txn_bin, txn, txn_len / 2)))
			quit(1, "Failed to hex2bin txn_bin");

		gen_hash(txn_bin, pool->txn_hashes + (32 * i), txn_len / 2);
		free(txn_bin);
	}
out:
	return ret;
}

static unsigned char *__gbt_merkleroot(struct pool *pool)
{
	unsigned char *merkle_hash;
	int i, txns;

	merkle_hash = calloc(32 * (pool->gbt_txns + 2), 1);
	if (unlikely(!merkle_hash))
		quit(1, "Failed to calloc merkle_hash in __gbt_merkleroot");

	gen_hash(pool->gbt_coinbase, merkle_hash, pool->coinbase_len);

	if (pool->gbt_txns)
		memcpy(merkle_hash + 32, pool->txn_hashes, pool->gbt_txns * 32);

	txns = pool->gbt_txns + 1;
	while (txns > 1) {
		if (txns % 2) {
			memcpy(&merkle_hash[txns * 32], &merkle_hash[(txns - 1) * 32], 32);
			txns++;
		}
		for (i = 0; i < txns; i += 2){
			unsigned char hashout[32];

			gen_hash(merkle_hash + (i * 32), hashout, 64);
			memcpy(merkle_hash + (i / 2 * 32), hashout, 32);
		}
		txns /= 2;
	}
	return merkle_hash;
}

static void calc_diff(struct work *work, int known);
static bool work_decode(struct pool *pool, struct work *work, json_t *val);

static void update_gbt(struct pool *pool)
{
	int rolltime;
	json_t *val;
	CURL *curl;

	curl = curl_easy_init();
	if (unlikely(!curl))
		quit (1, "CURL initialisation failed in update_gbt");

	val = json_rpc_call(curl, pool->rpc_url, pool->rpc_userpass,
			    pool->rpc_req, true, false, &rolltime, pool, false);

	if (val) {
		struct work *work = make_work();
		bool rc = work_decode(pool, work, val);

		total_getworks++;
		pool->getwork_requested++;
		if (rc) {
			applog(LOG_DEBUG, "Successfully retrieved and updated GBT from pool %u %s",
			       pool->pool_no, pool->rpc_url);
			cgtime(&pool->tv_idle);
		} else {
			applog(LOG_DEBUG, "Successfully retrieved but FAILED to decipher GBT from pool %u %s",
			       pool->pool_no, pool->rpc_url);
		}
		json_decref(val);
		free_work(work);
	} else {
		applog(LOG_DEBUG, "FAILED to update GBT from pool %u %s",
		       pool->pool_no, pool->rpc_url);
	}
	curl_easy_cleanup(curl);
}

static char *workpadding = "000000800000000000000000000000000000000000000000000000000000000000000000000000000000000080020000";

static void gen_gbt_work(struct pool *pool, struct work *work)
{
	unsigned char *merkleroot;
	struct timeval now;

	cgtime(&now);
	if (now.tv_sec - pool->tv_lastwork.tv_sec > 60)
		update_gbt(pool);

	cg_ilock(&pool->gbt_lock);
	__build_gbt_coinbase(pool);
	cg_dlock(&pool->gbt_lock);
	merkleroot = __gbt_merkleroot(pool);

	memcpy(work->data, &pool->gbt_version, 4);
	memcpy(work->data + 4, pool->previousblockhash, 32);
	memcpy(work->data + 4 + 32 + 32, &pool->curtime, 4);
	memcpy(work->data + 4 + 32 + 32 + 4, &pool->gbt_bits, 4);

	memcpy(work->target, pool->gbt_target, 32);

	work->gbt_coinbase = bin2hex(pool->gbt_coinbase, pool->coinbase_len);

	/* For encoding the block data on submission */
	work->gbt_txns = pool->gbt_txns + 1;

	if (pool->gbt_workid)
		work->job_id = strdup(pool->gbt_workid);
	cg_runlock(&pool->gbt_lock);

	memcpy(work->data + 4 + 32, merkleroot, 32);
	flip32(work->data + 4 + 32, merkleroot);
	free(merkleroot);
	memset(work->data + 4 + 32 + 32 + 4 + 4, 0, 4); /* nonce */

	hex2bin(work->data + 4 + 32 + 32 + 4 + 4 + 4, workpadding, 48);

	if (opt_debug) {
		char *header = bin2hex(work->data, 128);

		applog(LOG_DEBUG, "Generated GBT header %s", header);
		applog(LOG_DEBUG, "Work coinbase %s", work->gbt_coinbase);
		free(header);
	}

	calc_midstate(work);
	local_work++;
	work->pool = pool;
	work->gbt = true;
	work->id = total_work++;
	work->longpoll = false;
	work->getwork_mode = GETWORK_MODE_GBT;
	work->work_block = work_block;
	calc_diff(work, 0);
	cgtime(&work->tv_staged);
}

static bool gbt_decode(struct pool *pool, json_t *res_val)
{
	const char *previousblockhash;
	const char *target;
	const char *coinbasetxn;
	const char *longpollid;
	unsigned char hash_swap[32];
	int expires;
	int version;
	int curtime;
	bool submitold;
	const char *bits;
	const char *workid;

	previousblockhash = json_string_value(json_object_get(res_val, "previousblockhash"));
	target = json_string_value(json_object_get(res_val, "target"));
	coinbasetxn = json_string_value(json_object_get(json_object_get(res_val, "coinbasetxn"), "data"));
	longpollid = json_string_value(json_object_get(res_val, "longpollid"));
	expires = json_integer_value(json_object_get(res_val, "expires"));
	version = json_integer_value(json_object_get(res_val, "version"));
	curtime = json_integer_value(json_object_get(res_val, "curtime"));
	submitold = json_is_true(json_object_get(res_val, "submitold"));
	bits = json_string_value(json_object_get(res_val, "bits"));
	workid = json_string_value(json_object_get(res_val, "workid"));

	if (!previousblockhash || !target || !coinbasetxn || !longpollid ||
	    !expires || !version || !curtime || !bits) {
		applog(LOG_ERR, "JSON failed to decode GBT");
		return false;
	}

	applog(LOG_DEBUG, "previousblockhash: %s", previousblockhash);
	applog(LOG_DEBUG, "target: %s", target);
	applog(LOG_DEBUG, "coinbasetxn: %s", coinbasetxn);
	applog(LOG_DEBUG, "longpollid: %s", longpollid);
	applog(LOG_DEBUG, "expires: %d", expires);
	applog(LOG_DEBUG, "version: %d", version);
	applog(LOG_DEBUG, "curtime: %d", curtime);
	applog(LOG_DEBUG, "submitold: %s", submitold ? "true" : "false");
	applog(LOG_DEBUG, "bits: %s", bits);
	if (workid)
		applog(LOG_DEBUG, "workid: %s", workid);

	cg_wlock(&pool->gbt_lock);
	free(pool->coinbasetxn);
	pool->coinbasetxn = strdup(coinbasetxn);
	free(pool->longpollid);
	pool->longpollid = strdup(longpollid);
	free(pool->gbt_workid);
	if (workid)
		pool->gbt_workid = strdup(workid);
	else
		pool->gbt_workid = NULL;

	hex2bin(hash_swap, previousblockhash, 32);
	swap256(pool->previousblockhash, hash_swap);

	hex2bin(hash_swap, target, 32);
	swab256(pool->gbt_target, hash_swap);

	pool->gbt_expires = expires;
	pool->gbt_version = htobe32(version);
	pool->curtime = htobe32(curtime);
	pool->submit_old = submitold;

	hex2bin((unsigned char *)&pool->gbt_bits, bits, 4);

	__build_gbt_txns(pool, res_val);
	cg_wunlock(&pool->gbt_lock);

	return true;
}

static bool getwork_decode(json_t *res_val, struct work *work)
{
	if (unlikely(!jobj_binary(res_val, "data", work->data, sizeof(work->data), true))) {
		applog(LOG_ERR, "JSON inval data");
		return false;
	}

	if (!jobj_binary(res_val, "midstate", work->midstate, sizeof(work->midstate), false)) {
		// Calculate it ourselves
		applog(LOG_DEBUG, "Calculating midstate locally");
		calc_midstate(work);
	}

	if (unlikely(!jobj_binary(res_val, "target", work->target, sizeof(work->target), true))) {
		applog(LOG_ERR, "JSON inval target");
		return false;
	}
	return true;
}

/* Returns whether the pool supports local work generation or not. */
static bool pool_localgen(struct pool *pool)
{
	return (pool->has_gbt || pool->has_stratum);
}

static bool work_decode(struct pool *pool, struct work *work, json_t *val)
{
	json_t *res_val = json_object_get(val, "result");
	bool ret = false;

	cgtime(&pool->tv_lastwork);
	if (!res_val || json_is_null(res_val)) {
		applog(LOG_ERR, "JSON Failed to decode result");
		goto out;
	}

	if (pool->has_gbt) {
		if (unlikely(!gbt_decode(pool, res_val)))
			goto out;
		work->gbt = true;
		ret = true;
		goto out;
	} else if (unlikely(!getwork_decode(res_val, work)))
		goto out;

	memset(work->hash, 0, sizeof(work->hash));

	cgtime(&work->tv_staged);

	ret = true;

out:
	return ret;
}

int dev_from_id(int thr_id)
{
	struct cgpu_info *cgpu = get_thr_cgpu(thr_id);

	return cgpu->device_id;
}

/* Create an exponentially decaying average over the opt_log_interval */
void decay_time(double *f, double fadd, double fsecs)
{
	double ftotal, fprop;

	fprop = 1.0 - 1 / (exp(fsecs / (double)opt_log_interval));
	ftotal = 1.0 + fprop;
	*f += (fadd * fprop);
	*f /= ftotal;
}

static int __total_staged(void)
{
	return HASH_COUNT(staged_work);
}

static int total_staged(void)
{
	int ret;

	mutex_lock(stgd_lock);
	ret = __total_staged();
	mutex_unlock(stgd_lock);

	return ret;
}

#ifdef HAVE_CURSES
WINDOW *mainwin, *statuswin, *logwin;
#endif
double total_secs = 1.0;
static char statusline[256];
/* logstart is where the log window should start */
static int devcursor, logstart, logcursor;
#ifdef HAVE_CURSES
/* statusy is where the status window goes up to in cases where it won't fit at startup */
static int statusy;
#endif
#ifdef HAVE_OPENCL
struct cgpu_info gpus[MAX_GPUDEVICES]; /* Maximum number apparently possible */
#endif

#ifdef HAVE_CURSES
static inline void unlock_curses(void)
{
	mutex_unlock(&console_lock);
}

static inline void lock_curses(void)
{
	mutex_lock(&console_lock);
}

static bool curses_active_locked(void)
{
	bool ret;

	lock_curses();
	ret = curses_active;
	if (!ret)
		unlock_curses();
	return ret;
}
#endif

void tailsprintf(char *f, const char *fmt, ...)
{
	va_list ap;

	va_start(ap, fmt);
	vsprintf(f + strlen(f), fmt, ap);
	va_end(ap);
}

/* Convert a uint64_t value into a truncated string for displaying with its
 * associated suitable for Mega, Giga etc. Buf array needs to be long enough */
static void suffix_string(uint64_t val, char *buf, int sigdigits)
{
	const double  dkilo = 1000.0;
	const uint64_t kilo = 1000ull;
	const uint64_t mega = 1000000ull;
	const uint64_t giga = 1000000000ull;
	const uint64_t tera = 1000000000000ull;
	const uint64_t peta = 1000000000000000ull;
	const uint64_t exa  = 1000000000000000000ull;
	char suffix[2] = "";
	bool decimal = true;
	double dval;

	if (val >= exa) {
		val /= peta;
		dval = (double)val / dkilo;
		sprintf(suffix, "E");
	} else if (val >= peta) {
		val /= tera;
		dval = (double)val / dkilo;
		sprintf(suffix, "P");
	} else if (val >= tera) {
		val /= giga;
		dval = (double)val / dkilo;
		sprintf(suffix, "T");
	} else if (val >= giga) {
		val /= mega;
		dval = (double)val / dkilo;
		sprintf(suffix, "G");
	} else if (val >= mega) {
		val /= kilo;
		dval = (double)val / dkilo;
		sprintf(suffix, "M");
	} else if (val >= kilo) {
		dval = (double)val / dkilo;
		sprintf(suffix, "K");
	} else {
		dval = val;
		decimal = false;
	}

	if (!sigdigits) {
		if (decimal)
			sprintf(buf, "%.3g%s", dval, suffix);
		else
			sprintf(buf, "%d%s", (unsigned int)dval, suffix);
	} else {
		/* Always show sigdigits + 1, padded on right with zeroes
		 * followed by suffix */
		int ndigits = sigdigits - 1 - (dval > 0.0 ? floor(log10(dval)) : 0);

		sprintf(buf, "%*.*f%s", sigdigits + 1, ndigits, dval, suffix);
	}
}

static void get_statline(char *buf, struct cgpu_info *cgpu)
{
	char displayed_hashes[16], displayed_rolling[16];
	uint64_t dh64, dr64;
	struct timeval now;
	double dev_runtime, wu;

	if (cgpu->dev_start_tv.tv_sec == 0)
		dev_runtime = total_secs;
	else {
		cgtime(&now);
		dev_runtime = tdiff(&now, &(cgpu->dev_start_tv));
	}

	if (dev_runtime < 1.0)
		dev_runtime = 1.0;

	wu = cgpu->diff1 / dev_runtime * 60.0;

	dh64 = (double)cgpu->total_mhashes / dev_runtime * 1000000ull;
	dr64 = (double)cgpu->rolling * 1000000ull;
	suffix_string(dh64, displayed_hashes, 4);
	suffix_string(dr64, displayed_rolling, 4);

	sprintf(buf, "%s%d ", cgpu->drv->name, cgpu->device_id);
	cgpu->drv->get_statline_before(buf, cgpu);
	tailsprintf(buf, "(%ds):%s (avg):%sh/s | A:%.0f R:%.0f HW:%d WU:%.1f/m",
		opt_log_interval,
		displayed_rolling,
		displayed_hashes,
		cgpu->diff_accepted,
		cgpu->diff_rejected,
		cgpu->hw_errors,
		wu);
	cgpu->drv->get_statline(buf, cgpu);
}

static void text_print_status(int thr_id)
{
	struct cgpu_info *cgpu;
	char logline[256];

	cgpu = get_thr_cgpu(thr_id);
	if (cgpu) {
		get_statline(logline, cgpu);
		printf("%s\n", logline);
	}
}

#ifdef HAVE_CURSES
/* Must be called with curses mutex lock held and curses_active */
static void curses_print_status(void)
{
	struct pool *pool = current_pool();

	wattron(statuswin, A_BOLD);
	mvwprintw(statuswin, 0, 0, " " PACKAGE " version " VERSION " - Started: %s", datestamp);
	wattroff(statuswin, A_BOLD);
	mvwhline(statuswin, 1, 0, '-', 80);
	mvwprintw(statuswin, 2, 0, " %s", statusline);
	wclrtoeol(statuswin);
	mvwprintw(statuswin, 3, 0, " ST: %d  SS: %d  NB: %d  LW: %d  GF: %d  RF: %d",
		total_staged(), total_stale, new_blocks,
		local_work, total_go, total_ro);
	wclrtoeol(statuswin);
	if ((pool_strategy == POOL_LOADBALANCE  || pool_strategy == POOL_BALANCE) && total_pools > 1) {
		mvwprintw(statuswin, 4, 0, " Connected to multiple pools with%s LP",
			have_longpoll ? "": "out");
	} else if (pool->has_stratum) {
		mvwprintw(statuswin, 4, 0, " Connected to %s diff %s with stratum as user %s",
			pool->sockaddr_url, pool->diff, pool->rpc_user);
	} else {
		mvwprintw(statuswin, 4, 0, " Connected to %s diff %s with%s %s as user %s",
			pool->sockaddr_url, pool->diff, have_longpoll ? "": "out",
			pool->has_gbt ? "GBT" : "LP", pool->rpc_user);
	}
	wclrtoeol(statuswin);
	mvwprintw(statuswin, 5, 0, " Block: %s...  Diff:%s  Started: %s  Best share: %s   ",
		  current_hash, block_diff, blocktime, best_share);
	mvwhline(statuswin, 6, 0, '-', 80);
	mvwhline(statuswin, statusy - 1, 0, '-', 80);
	mvwprintw(statuswin, devcursor - 1, 1, "[P]ool management %s[S]ettings [D]isplay options [Q]uit",
		have_opencl ? "[G]PU management " : "");
}

static void adj_width(int var, int *length)
{
	if ((int)(log10(var) + 1) > *length)
		(*length)++;
}

static void adj_fwidth(float var, int *length)
{
	if ((int)(log10(var) + 1) > *length)
		(*length)++;
}

static int dev_width;

static void curses_print_devstatus(struct cgpu_info *cgpu, int count)
{
	static int dawidth = 1, drwidth = 1, hwwidth = 1, wuwidth = 1;
	char logline[256];
	char displayed_hashes[16], displayed_rolling[16];
	uint64_t dh64, dr64;
	struct timeval now;
	double dev_runtime, wu;

	if (opt_compact)
		return;

	if (devcursor + count > LINES - 2)
		return;

	if (count >= most_devices)
		return;

	if (cgpu->dev_start_tv.tv_sec == 0)
		dev_runtime = total_secs;
	else {
		cgtime(&now);
		dev_runtime = tdiff(&now, &(cgpu->dev_start_tv));
	}

	if (dev_runtime < 1.0)
		dev_runtime = 1.0;

	cgpu->utility = cgpu->accepted / dev_runtime * 60;
	wu = cgpu->diff1 / dev_runtime * 60;

	wmove(statuswin,devcursor + count, 0);
	wprintw(statuswin, " %s %*d: ", cgpu->drv->name, dev_width, cgpu->device_id);
	logline[0] = '\0';
	cgpu->drv->get_statline_before(logline, cgpu);
	wprintw(statuswin, "%s", logline);

	dh64 = (double)cgpu->total_mhashes / dev_runtime * 1000000ull;
	dr64 = (double)cgpu->rolling * 1000000ull;
	suffix_string(dh64, displayed_hashes, 4);
	suffix_string(dr64, displayed_rolling, 4);

#ifdef USE_USBUTILS
	if (cgpu->usbinfo.nodev)
		wprintw(statuswin, "ZOMBIE");
	else
#endif
	if (cgpu->status == LIFE_DEAD)
		wprintw(statuswin, "DEAD  ");
	else if (cgpu->status == LIFE_SICK)
		wprintw(statuswin, "SICK  ");
	else if (cgpu->deven == DEV_DISABLED)
		wprintw(statuswin, "OFF   ");
	else if (cgpu->deven == DEV_RECOVER)
		wprintw(statuswin, "REST  ");
	else
		wprintw(statuswin, "%6s", displayed_rolling);
	adj_fwidth(cgpu->diff_accepted, &dawidth);
	adj_fwidth(cgpu->diff_rejected, &drwidth);
	adj_width(cgpu->hw_errors, &hwwidth);
	adj_width(wu, &wuwidth);

	wprintw(statuswin, "/%6sh/s | A:%*.0f R:%*.0f HW:%*d WU:%*.1f/m",
			displayed_hashes,
			dawidth, cgpu->diff_accepted,
			drwidth, cgpu->diff_rejected,
			hwwidth, cgpu->hw_errors,
			wuwidth + 3, wu);

	logline[0] = '\0';
	cgpu->drv->get_statline(logline, cgpu);
	wprintw(statuswin, "%s", logline);

	wclrtoeol(statuswin);
}
#endif

static void print_status(int thr_id)
{
	if (!curses_active)
		text_print_status(thr_id);
}

#ifdef HAVE_CURSES
/* Check for window resize. Called with curses mutex locked */
static inline void change_logwinsize(void)
{
	int x, y, logx, logy;

	getmaxyx(mainwin, y, x);
	if (x < 80 || y < 25)
		return;

	if (y > statusy + 2 && statusy < logstart) {
		if (y - 2 < logstart)
			statusy = y - 2;
		else
			statusy = logstart;
		logcursor = statusy + 1;
		mvwin(logwin, logcursor, 0);
		wresize(statuswin, statusy, x);
	}

	y -= logcursor;
	getmaxyx(logwin, logy, logx);
	/* Detect screen size change */
	if (x != logx || y != logy)
		wresize(logwin, y, x);
}

static void check_winsizes(void)
{
	if (!use_curses)
		return;
	if (curses_active_locked()) {
		int y, x;

		erase();
		x = getmaxx(statuswin);
		if (logstart > LINES - 2)
			statusy = LINES - 2;
		else
			statusy = logstart;
		logcursor = statusy + 1;
		wresize(statuswin, statusy, x);
		getmaxyx(mainwin, y, x);
		y -= logcursor;
		wresize(logwin, y, x);
		mvwin(logwin, logcursor, 0);
		unlock_curses();
	}
}

static void switch_logsize(void)
{
	if (curses_active_locked()) {
		if (opt_compact) {
			logstart = devcursor + 1;
			logcursor = logstart + 1;
		} else {
			logstart = devcursor + most_devices + 1;
			logcursor = logstart + 1;
		}
		unlock_curses();
	}
	check_winsizes();
}

/* For mandatory printing when mutex is already locked */
void _wlog(const char *str)
{
	wprintw(logwin, "%s", str);
}

/* Mandatory printing */
void _wlogprint(const char *str)
{
	if (curses_active_locked()) {
		wprintw(logwin, "%s", str);
		unlock_curses();
	}
}
#else
static void switch_logsize(void)
{
}
#endif

#ifdef HAVE_CURSES
bool log_curses_only(int prio, const char *datetime, const char *str)
{
	bool high_prio;

	high_prio = (prio == LOG_WARNING || prio == LOG_ERR);

	if (curses_active_locked()) {
		if (!opt_loginput || high_prio) {
			wprintw(logwin, "%s%s\n", datetime, str);
			if (high_prio) {
				touchwin(logwin);
				wrefresh(logwin);
			}
		}
		unlock_curses();
		return true;
	}
	return false;
}

void clear_logwin(void)
{
	if (curses_active_locked()) {
		erase();
		wclear(logwin);
		unlock_curses();
	}
}

void logwin_update(void)
{
	if (curses_active_locked()) {
		touchwin(logwin);
		wrefresh(logwin);
		unlock_curses();
	}
}
#endif

static void enable_pool(struct pool *pool)
{
	if (pool->enabled != POOL_ENABLED) {
		enabled_pools++;
		pool->enabled = POOL_ENABLED;
	}
}

#ifdef HAVE_CURSES
static void disable_pool(struct pool *pool)
{
	if (pool->enabled == POOL_ENABLED)
		enabled_pools--;
	pool->enabled = POOL_DISABLED;
}
#endif

static void reject_pool(struct pool *pool)
{
	if (pool->enabled == POOL_ENABLED)
		enabled_pools--;
	pool->enabled = POOL_REJECTING;
}

static void restart_threads(void);

/* Theoretically threads could race when modifying accepted and
 * rejected values but the chance of two submits completing at the
 * same time is zero so there is no point adding extra locking */
static void
share_result(json_t *val, json_t *res, json_t *err, const struct work *work,
	     char *hashshow, bool resubmit, char *worktime)
{
	struct pool *pool = work->pool;
	struct cgpu_info *cgpu;

	cgpu = get_thr_cgpu(work->thr_id);

	if (json_is_true(res) || (work->gbt && json_is_null(res))) {
		mutex_lock(&stats_lock);
		cgpu->accepted++;
		total_accepted++;
		pool->accepted++;
		cgpu->diff_accepted += work->work_difficulty;
		total_diff_accepted += work->work_difficulty;
		pool->diff_accepted += work->work_difficulty;
		mutex_unlock(&stats_lock);

		pool->seq_rejects = 0;
		cgpu->last_share_pool = pool->pool_no;
		cgpu->last_share_pool_time = time(NULL);
		cgpu->last_share_diff = work->work_difficulty;
		pool->last_share_time = cgpu->last_share_pool_time;
		pool->last_share_diff = work->work_difficulty;
		applog(LOG_DEBUG, "PROOF OF WORK RESULT: true (yay!!!)");
		if (!QUIET) {
			if (total_pools > 1)
				applog(LOG_NOTICE, "Accepted %s %s %d pool %d %s%s",
				       hashshow, cgpu->drv->name, cgpu->device_id, work->pool->pool_no, resubmit ? "(resubmit)" : "", worktime);
			else
				applog(LOG_NOTICE, "Accepted %s %s %d %s%s",
				       hashshow, cgpu->drv->name, cgpu->device_id, resubmit ? "(resubmit)" : "", worktime);
		}
		sharelog("accept", work);
		if (opt_shares && total_accepted >= opt_shares) {
			applog(LOG_WARNING, "Successfully mined %d accepted shares as requested and exiting.", opt_shares);
			kill_work();
			return;
		}

		/* Detect if a pool that has been temporarily disabled for
		 * continually rejecting shares has started accepting shares.
		 * This will only happen with the work returned from a
		 * longpoll */
		if (unlikely(pool->enabled == POOL_REJECTING)) {
			applog(LOG_WARNING, "Rejecting pool %d now accepting shares, re-enabling!", pool->pool_no);
			enable_pool(pool);
			switch_pools(NULL);
		}
		/* If we know we found the block we know better than anyone
		 * that new work is needed. */
		if (unlikely(work->block))
			restart_threads();
	} else {
		mutex_lock(&stats_lock);
		cgpu->rejected++;
		total_rejected++;
		pool->rejected++;
		cgpu->diff_rejected += work->work_difficulty;
		total_diff_rejected += work->work_difficulty;
		pool->diff_rejected += work->work_difficulty;
		pool->seq_rejects++;
		mutex_unlock(&stats_lock);

		applog(LOG_DEBUG, "PROOF OF WORK RESULT: false (booooo)");
		if (!QUIET) {
			char where[20];
			char disposition[36] = "reject";
			char reason[32];

			strcpy(reason, "");
			if (total_pools > 1)
				sprintf(where, "pool %d", work->pool->pool_no);
			else
				strcpy(where, "");

			if (!work->gbt)
				res = json_object_get(val, "reject-reason");
			if (res) {
				const char *reasontmp = json_string_value(res);

				size_t reasonLen = strlen(reasontmp);
				if (reasonLen > 28)
					reasonLen = 28;
				reason[0] = ' '; reason[1] = '(';
				memcpy(2 + reason, reasontmp, reasonLen);
				reason[reasonLen + 2] = ')'; reason[reasonLen + 3] = '\0';
				memcpy(disposition + 7, reasontmp, reasonLen);
				disposition[6] = ':'; disposition[reasonLen + 7] = '\0';
			} else if (work->stratum && err && json_is_array(err)) {
				json_t *reason_val = json_array_get(err, 1);
				char *reason_str;

				if (reason_val && json_is_string(reason_val)) {
					reason_str = (char *)json_string_value(reason_val);
					snprintf(reason, 31, " (%s)", reason_str);
				}
			}

			applog(LOG_NOTICE, "Rejected %s %s %d %s%s %s%s",
			       hashshow, cgpu->drv->name, cgpu->device_id, where, reason, resubmit ? "(resubmit)" : "", worktime);
			sharelog(disposition, work);
		}

		/* Once we have more than a nominal amount of sequential rejects,
		 * at least 10 and more than 3 mins at the current utility,
		 * disable the pool because some pool error is likely to have
		 * ensued. Do not do this if we know the share just happened to
		 * be stale due to networking delays.
		 */
		if (pool->seq_rejects > 10 && !work->stale && opt_disable_pool && enabled_pools > 1) {
			double utility = total_accepted / total_secs * 60;

			if (pool->seq_rejects > utility * 3) {
				applog(LOG_WARNING, "Pool %d rejected %d sequential shares, disabling!",
				       pool->pool_no, pool->seq_rejects);
				reject_pool(pool);
				if (pool == current_pool())
					switch_pools(NULL);
				pool->seq_rejects = 0;
			}
		}
	}
}

static bool submit_upstream_work(struct work *work, CURL *curl, bool resubmit)
{
	char *hexstr = NULL;
	json_t *val, *res, *err;
	char *s;
	bool rc = false;
	int thr_id = work->thr_id;
	struct cgpu_info *cgpu;
	struct pool *pool = work->pool;
	int rolltime;
	struct timeval tv_submit, tv_submit_reply;
	char hashshow[64 + 4] = "";
	char worktime[200] = "";
	struct timeval now;
	double dev_runtime;

	cgpu = get_thr_cgpu(thr_id);

	endian_flip128(work->data, work->data);

	/* build hex string */
	hexstr = bin2hex(work->data, sizeof(work->data));

	/* build JSON-RPC request */
	if (work->gbt) {
		char *gbt_block, *varint;
		unsigned char data[80];

		flip80(data, work->data);
		gbt_block = bin2hex(data, 80);

		if (work->gbt_txns < 0xfd) {
			uint8_t val = work->gbt_txns;

			varint = bin2hex((const unsigned char *)&val, 1);
		} else if (work->gbt_txns <= 0xffff) {
			uint16_t val = htole16(work->gbt_txns);

			gbt_block = realloc_strcat(gbt_block, "fd");
			varint = bin2hex((const unsigned char *)&val, 2);
		} else {
			uint32_t val = htole32(work->gbt_txns);

			gbt_block = realloc_strcat(gbt_block, "fe");
			varint = bin2hex((const unsigned char *)&val, 4);
		}
		gbt_block = realloc_strcat(gbt_block, varint);
		free(varint);
		gbt_block = realloc_strcat(gbt_block, work->gbt_coinbase);

		s = strdup("{\"id\": 0, \"method\": \"submitblock\", \"params\": [\"");
		s = realloc_strcat(s, gbt_block);
		if (work->job_id) {
			s = realloc_strcat(s, "\", {\"workid\": \"");
			s = realloc_strcat(s, work->job_id);
			s = realloc_strcat(s, "\"}]}");
		} else
			s = realloc_strcat(s, "\", {}]}");
		free(gbt_block);
	} else {
		s = strdup("{\"method\": \"getwork\", \"params\": [ \"");
		s = realloc_strcat(s, hexstr);
		s = realloc_strcat(s, "\" ], \"id\":1}");
	}
	applog(LOG_DEBUG, "DBG: sending %s submit RPC call: %s", pool->rpc_url, s);
	s = realloc_strcat(s, "\n");

	cgtime(&tv_submit);
	/* issue JSON-RPC request */
	val = json_rpc_call(curl, pool->rpc_url, pool->rpc_userpass, s, false, false, &rolltime, pool, true);
	cgtime(&tv_submit_reply);
	free(s);

	if (unlikely(!val)) {
		applog(LOG_INFO, "submit_upstream_work json_rpc_call failed");
		if (!pool_tset(pool, &pool->submit_fail)) {
			total_ro++;
			pool->remotefail_occasions++;
			if (opt_lowmem) {
				applog(LOG_WARNING, "Pool %d communication failure, discarding shares", pool->pool_no);
				goto out;
			}
			applog(LOG_WARNING, "Pool %d communication failure, caching submissions", pool->pool_no);
		}
		nmsleep(5000);
		goto out;
	} else if (pool_tclear(pool, &pool->submit_fail))
		applog(LOG_WARNING, "Pool %d communication resumed, submitting work", pool->pool_no);

	res = json_object_get(val, "result");
	err = json_object_get(val, "error");

	if (!QUIET) {
		int intdiff = floor(work->work_difficulty);
		char diffdisp[16], *outhash;
		unsigned char rhash[32];

		swab256(rhash, work->hash);
		if (opt_scrypt)
			outhash = bin2hex(rhash + 2, 4);
		else
			outhash = bin2hex(rhash + 4, 4);
		suffix_string(work->share_diff, diffdisp, 0);
		sprintf(hashshow, "%s Diff %s/%d%s", outhash, diffdisp, intdiff,
			work->block? " BLOCK!" : "");
		free(outhash);

		if (opt_worktime) {
			char workclone[20];
			struct tm *tm, tm_getwork, tm_submit_reply;
			double getwork_time = tdiff((struct timeval *)&(work->tv_getwork_reply),
							(struct timeval *)&(work->tv_getwork));
			double getwork_to_work = tdiff((struct timeval *)&(work->tv_work_start),
							(struct timeval *)&(work->tv_getwork_reply));
			double work_time = tdiff((struct timeval *)&(work->tv_work_found),
							(struct timeval *)&(work->tv_work_start));
			double work_to_submit = tdiff(&tv_submit,
							(struct timeval *)&(work->tv_work_found));
			double submit_time = tdiff(&tv_submit_reply, &tv_submit);
			int diffplaces = 3;

			time_t tmp_time = work->tv_getwork.tv_sec;
			tm = localtime(&tmp_time);
			memcpy(&tm_getwork, tm, sizeof(struct tm));
			tmp_time = tv_submit_reply.tv_sec;
			tm = localtime(&tmp_time);
			memcpy(&tm_submit_reply, tm, sizeof(struct tm));

			if (work->clone) {
				sprintf(workclone, "C:%1.3f",
					tdiff((struct timeval *)&(work->tv_cloned),
						(struct timeval *)&(work->tv_getwork_reply)));
			}
			else
				strcpy(workclone, "O");

			if (work->work_difficulty < 1)
				diffplaces = 6;

			sprintf(worktime, " <-%08lx.%08lx M:%c D:%1.*f G:%02d:%02d:%02d:%1.3f %s (%1.3f) W:%1.3f (%1.3f) S:%1.3f R:%02d:%02d:%02d",
				(unsigned long)swab32(*(uint32_t *)&(work->data[opt_scrypt ? 32 : 28])),
				(unsigned long)swab32(*(uint32_t *)&(work->data[opt_scrypt ? 28 : 24])),
				work->getwork_mode, diffplaces, work->work_difficulty,
				tm_getwork.tm_hour, tm_getwork.tm_min,
				tm_getwork.tm_sec, getwork_time, workclone,
				getwork_to_work, work_time, work_to_submit, submit_time,
				tm_submit_reply.tm_hour, tm_submit_reply.tm_min,
				tm_submit_reply.tm_sec);
		}
	}

	share_result(val, res, err, work, hashshow, resubmit, worktime);

	if (cgpu->dev_start_tv.tv_sec == 0)
		dev_runtime = total_secs;
	else {
		cgtime(&now);
		dev_runtime = tdiff(&now, &(cgpu->dev_start_tv));
	}

	if (dev_runtime < 1.0)
		dev_runtime = 1.0;

	cgpu->utility = cgpu->accepted / dev_runtime * 60;

	if (!opt_realquiet)
		print_status(thr_id);
	if (!want_per_device_stats) {
		char logline[256];

		get_statline(logline, cgpu);
		applog(LOG_INFO, "%s", logline);
	}

	json_decref(val);

	rc = true;
out:
	free(hexstr);
	return rc;
}

/* Specifies whether we can use this pool for work or not. */
static bool pool_unworkable(struct pool *pool)
{
	if (pool->idle)
		return true;
	if (pool->enabled != POOL_ENABLED)
		return true;
	if (pool->has_stratum && !pool->stratum_active)
		return true;
	return false;
}

/* In balanced mode, the amount of diff1 solutions per pool is monitored as a
 * rolling average per 10 minutes and if pools start getting more, it biases
 * away from them to distribute work evenly. The share count is reset to the
 * rolling average every 10 minutes to not send all work to one pool after it
 * has been disabled/out for an extended period. */
static struct pool *select_balanced(struct pool *cp)
{
	int i, lowest = cp->shares;
	struct pool *ret = cp;

	for (i = 0; i < total_pools; i++) {
		struct pool *pool = pools[i];

		if (pool_unworkable(pool))
			continue;
		if (pool->shares < lowest) {
			lowest = pool->shares;
			ret = pool;
		}
	}

	ret->shares++;
	return ret;
}

/* Select any active pool in a rotating fashion when loadbalance is chosen */
static inline struct pool *select_pool(bool lagging)
{
	static int rotating_pool = 0;
	struct pool *pool, *cp;
	int tested;

	cp = current_pool();

	if (pool_strategy == POOL_BALANCE)
		return select_balanced(cp);

	if (pool_strategy != POOL_LOADBALANCE && (!lagging || opt_fail_only))
		pool = cp;
	else
		pool = NULL;

	/* Try to find the first pool in the rotation that is usable */
	tested = 0;
	while (!pool && tested++ < total_pools) {
		if (++rotating_pool >= total_pools)
			rotating_pool = 0;
		pool = pools[rotating_pool];
		if (!pool_unworkable(pool))
			break;
		pool = NULL;
	}
	/* If still nothing is usable, use the current pool */
	if (!pool)
		pool = cp;

	return pool;
}

static double DIFFEXACTONE = 26959946667150639794667015087019630673637144422540572481103610249215.0;
static const uint64_t diffone = 0xFFFF000000000000ull;

/*
 * Calculate the work share difficulty
 */
static void calc_diff(struct work *work, int known)
{
	struct cgminer_pool_stats *pool_stats = &(work->pool->cgminer_pool_stats);
	double difficulty;

	if (opt_scrypt) {
		uint64_t *data64, d64;
		char rtarget[32];

		swab256(rtarget, work->target);
		data64 = (uint64_t *)(rtarget + 2);
		d64 = be64toh(*data64);
		if (unlikely(!d64))
			d64 = 1;
		work->work_difficulty = diffone / d64;
	} else if (!known) {
		double targ = 0;
		int i;

		for (i = 31; i >= 0; i--) {
			targ *= 256;
			targ += work->target[i];
		}

		work->work_difficulty = DIFFEXACTONE / (targ ? : DIFFEXACTONE);
	} else
		work->work_difficulty = known;
	difficulty = work->work_difficulty;

	pool_stats->last_diff = difficulty;
	suffix_string((uint64_t)difficulty, work->pool->diff, 0);

	if (difficulty == pool_stats->min_diff)
		pool_stats->min_diff_count++;
	else if (difficulty < pool_stats->min_diff || pool_stats->min_diff == 0) {
		pool_stats->min_diff = difficulty;
		pool_stats->min_diff_count = 1;
	}

	if (difficulty == pool_stats->max_diff)
		pool_stats->max_diff_count++;
	else if (difficulty > pool_stats->max_diff) {
		pool_stats->max_diff = difficulty;
		pool_stats->max_diff_count = 1;
	}
}

static void get_benchmark_work(struct work *work)
{
	// Use a random work block pulled from a pool
	static uint8_t bench_block[] = { CGMINER_BENCHMARK_BLOCK };

	size_t bench_size = sizeof(*work);
	size_t work_size = sizeof(bench_block);
	size_t min_size = (work_size < bench_size ? work_size : bench_size);
	memset(work, 0, sizeof(*work));
	memcpy(work, &bench_block, min_size);
	work->mandatory = true;
	work->pool = pools[0];
	cgtime(&work->tv_getwork);
	copy_time(&work->tv_getwork_reply, &work->tv_getwork);
	work->getwork_mode = GETWORK_MODE_BENCHMARK;
	calc_diff(work, 0);
}

static bool get_upstream_work(struct work *work, CURL *curl)
{
	struct pool *pool = work->pool;
	struct cgminer_pool_stats *pool_stats = &(pool->cgminer_pool_stats);
	struct timeval tv_elapsed;
	json_t *val = NULL;
	bool rc = false;
	char *url;

	applog(LOG_DEBUG, "DBG: sending %s get RPC call: %s", pool->rpc_url, pool->rpc_req);

	url = pool->rpc_url;

	cgtime(&work->tv_getwork);

	val = json_rpc_call(curl, url, pool->rpc_userpass, pool->rpc_req, false,
			    false, &work->rolltime, pool, false);
	pool_stats->getwork_attempts++;

	if (likely(val)) {
		rc = work_decode(pool, work, val);
		if (unlikely(!rc))
			applog(LOG_DEBUG, "Failed to decode work in get_upstream_work");
	} else
		applog(LOG_DEBUG, "Failed json_rpc_call in get_upstream_work");

	cgtime(&work->tv_getwork_reply);
	timersub(&(work->tv_getwork_reply), &(work->tv_getwork), &tv_elapsed);
	pool_stats->getwork_wait_rolling += ((double)tv_elapsed.tv_sec + ((double)tv_elapsed.tv_usec / 1000000)) * 0.63;
	pool_stats->getwork_wait_rolling /= 1.63;

	timeradd(&tv_elapsed, &(pool_stats->getwork_wait), &(pool_stats->getwork_wait));
	if (timercmp(&tv_elapsed, &(pool_stats->getwork_wait_max), >)) {
		pool_stats->getwork_wait_max.tv_sec = tv_elapsed.tv_sec;
		pool_stats->getwork_wait_max.tv_usec = tv_elapsed.tv_usec;
	}
	if (timercmp(&tv_elapsed, &(pool_stats->getwork_wait_min), <)) {
		pool_stats->getwork_wait_min.tv_sec = tv_elapsed.tv_sec;
		pool_stats->getwork_wait_min.tv_usec = tv_elapsed.tv_usec;
	}
	pool_stats->getwork_calls++;

	work->pool = pool;
	work->longpoll = false;
	work->getwork_mode = GETWORK_MODE_POOL;
	calc_diff(work, 0);
	total_getworks++;
	pool->getwork_requested++;

	if (likely(val))
		json_decref(val);

	return rc;
}

#ifdef HAVE_CURSES
static void disable_curses(void)
{
	if (curses_active_locked()) {
		use_curses = false;
		curses_active = false;
		leaveok(logwin, false);
		leaveok(statuswin, false);
		leaveok(mainwin, false);
		nocbreak();
		echo();
		delwin(logwin);
		delwin(statuswin);
		delwin(mainwin);
		endwin();
#ifdef WIN32
		// Move the cursor to after curses output.
		HANDLE hout = GetStdHandle(STD_OUTPUT_HANDLE);
		CONSOLE_SCREEN_BUFFER_INFO csbi;
		COORD coord;

		if (GetConsoleScreenBufferInfo(hout, &csbi)) {
			coord.X = 0;
			coord.Y = csbi.dwSize.Y - 1;
			SetConsoleCursorPosition(hout, coord);
		}
#endif
		unlock_curses();
	}
}
#endif

static void __kill_work(void)
{
	struct thr_info *thr;
	int i;

	if (!successful_connect)
		return;

	applog(LOG_INFO, "Received kill message");

#ifdef USE_USBUTILS
	/* Best to get rid of it first so it doesn't
	 * try to create any new devices */
	if (!opt_scrypt) {
		applog(LOG_DEBUG, "Killing off HotPlug thread");
		thr = &control_thr[hotplug_thr_id];
		thr_info_cancel(thr);
	}
#endif

	applog(LOG_DEBUG, "Killing off watchpool thread");
	/* Kill the watchpool thread */
	thr = &control_thr[watchpool_thr_id];
	thr_info_cancel(thr);

	applog(LOG_DEBUG, "Killing off watchdog thread");
	/* Kill the watchdog thread */
	thr = &control_thr[watchdog_thr_id];
	thr_info_cancel(thr);

	applog(LOG_DEBUG, "Shutting down mining threads");
	for (i = 0; i < mining_threads; i++) {
		struct cgpu_info *cgpu;

		thr = get_thread(i);
		if (!thr)
			continue;
		cgpu = thr->cgpu;
		if (!cgpu)
			continue;

		cgpu->shutdown = true;
	}

	sleep(1);

	applog(LOG_DEBUG, "Killing off mining threads");
	/* Kill the mining threads*/
	for (i = 0; i < mining_threads; i++) {
		pthread_t *pth = NULL;

		thr = get_thread(i);
		if (thr && PTH(thr) != 0L)
			pth = &thr->pth;
		thr_info_cancel(thr);
#ifndef WIN32
		if (pth && *pth)
			pthread_join(*pth, NULL);
#else
		if (pth && pth->p)
			pthread_join(*pth, NULL);
#endif
	}

	applog(LOG_DEBUG, "Killing off stage thread");
	/* Stop the others */
	thr = &control_thr[stage_thr_id];
	thr_info_cancel(thr);

	applog(LOG_DEBUG, "Killing off API thread");
	thr = &control_thr[api_thr_id];
	thr_info_cancel(thr);

#ifdef USE_USBUTILS
	/* Release USB resources in case it's a restart
	 * and not a QUIT */
	if (!opt_scrypt) {
		applog(LOG_DEBUG, "Releasing all USB devices");
		usb_cleanup();

		applog(LOG_DEBUG, "Killing off usbres thread");
		thr = &control_thr[usbres_thr_id];
		thr_info_cancel(thr);
	}
#endif

}

/* This should be the common exit path */
void kill_work(void)
{
	__kill_work();

	quit(0, "Shutdown signal received.");
}

static
#ifdef WIN32
const
#endif
char **initial_args;

static void clean_up(void);

void app_restart(void)
{
	applog(LOG_WARNING, "Attempting to restart %s", packagename);

	__kill_work();
	clean_up();

#if defined(unix) || defined(__APPLE__)
	if (forkpid > 0) {
		kill(forkpid, SIGTERM);
		forkpid = 0;
	}
#endif

	execv(initial_args[0], (EXECV_2ND_ARG_TYPE)initial_args);
	applog(LOG_WARNING, "Failed to restart application");
}

static void sighandler(int __maybe_unused sig)
{
	/* Restore signal handlers so we can still quit if kill_work fails */
	sigaction(SIGTERM, &termhandler, NULL);
	sigaction(SIGINT, &inthandler, NULL);
	kill_work();
}

/* Called with pool_lock held. Recruit an extra curl if none are available for
 * this pool. */
static void recruit_curl(struct pool *pool)
{
	struct curl_ent *ce = calloc(sizeof(struct curl_ent), 1);

	if (unlikely(!ce))
		quit(1, "Failed to calloc in recruit_curl");

	ce->curl = curl_easy_init();
	if (unlikely(!ce->curl))
		quit(1, "Failed to init in recruit_curl");

	list_add(&ce->node, &pool->curlring);
	pool->curls++;
}

/* Grab an available curl if there is one. If not, then recruit extra curls
 * unless we are in a submit_fail situation, or we have opt_delaynet enabled
 * and there are already 5 curls in circulation. Limit total number to the
 * number of mining threads per pool as well to prevent blasting a pool during
 * network delays/outages. */
static struct curl_ent *pop_curl_entry(struct pool *pool)
{
	int curl_limit = opt_delaynet ? 5 : (mining_threads + opt_queue) * 2;
	bool recruited = false;
	struct curl_ent *ce;

	mutex_lock(&pool->pool_lock);
retry:
	if (!pool->curls) {
		recruit_curl(pool);
		recruited = true;
	} else if (list_empty(&pool->curlring)) {
		if (pool->curls >= curl_limit) {
			pthread_cond_wait(&pool->cr_cond, &pool->pool_lock);
			goto retry;
		} else {
			recruit_curl(pool);
			recruited = true;
		}
	}
	ce = list_entry(pool->curlring.next, struct curl_ent, node);
	list_del(&ce->node);
	mutex_unlock(&pool->pool_lock);

	if (recruited)
		applog(LOG_DEBUG, "Recruited curl for pool %d", pool->pool_no);
	return ce;
}

static void push_curl_entry(struct curl_ent *ce, struct pool *pool)
{
	mutex_lock(&pool->pool_lock);
	list_add_tail(&ce->node, &pool->curlring);
	cgtime(&ce->tv);
	pthread_cond_broadcast(&pool->cr_cond);
	mutex_unlock(&pool->pool_lock);
}

static bool stale_work(struct work *work, bool share);

static inline bool should_roll(struct work *work)
{
	struct timeval now;
	time_t expiry;

	if (work->pool != current_pool() && pool_strategy != POOL_LOADBALANCE && pool_strategy != POOL_BALANCE)
		return false;

	if (work->rolltime > opt_scantime)
		expiry = work->rolltime;
	else
		expiry = opt_scantime;
	expiry = expiry * 2 / 3;

	/* We shouldn't roll if we're unlikely to get one shares' duration
	 * work out of doing so */
	cgtime(&now);
	if (now.tv_sec - work->tv_staged.tv_sec > expiry)
		return false;
	
	return true;
}

/* Limit rolls to 7000 to not beyond 2 hours in the future where bitcoind will
 * reject blocks as invalid. */
static inline bool can_roll(struct work *work)
{
	return (!work->stratum && work->pool && work->rolltime && !work->clone &&
		work->rolls < 7000 && !stale_work(work, false));
}

static void roll_work(struct work *work)
{
	uint32_t *work_ntime;
	uint32_t ntime;

	work_ntime = (uint32_t *)(work->data + 68);
	ntime = be32toh(*work_ntime);
	ntime++;
	*work_ntime = htobe32(ntime);
	local_work++;
	work->rolls++;
	work->blk.nonce = 0;
	applog(LOG_DEBUG, "Successfully rolled work");

	/* This is now a different work item so it needs a different ID for the
	 * hashtable */
	work->id = total_work++;
}

/* Duplicates any dynamically allocated arrays within the work struct to
 * prevent a copied work struct from freeing ram belonging to another struct */
void __copy_work(struct work *work, struct work *base_work)
{
	int id = work->id;

	clean_work(work);
	memcpy(work, base_work, sizeof(struct work));
	/* Keep the unique new id assigned during make_work to prevent copied
	 * work from having the same id. */
	work->id = id;
	if (base_work->job_id)
		work->job_id = strdup(base_work->job_id);
	if (base_work->nonce1)
		work->nonce1 = strdup(base_work->nonce1);
	if (base_work->nonce2)
		work->nonce2 = strdup(base_work->nonce2);
	if (base_work->ntime)
		work->ntime = strdup(base_work->ntime);
	if (base_work->gbt_coinbase)
		work->gbt_coinbase = strdup(base_work->gbt_coinbase);
}

/* Generates a copy of an existing work struct, creating fresh heap allocations
 * for all dynamically allocated arrays within the struct */
struct work *copy_work(struct work *base_work)
{
	struct work *work = make_work();

	__copy_work(work, base_work);

	return work;
}

static struct work *make_clone(struct work *work)
{
	struct work *work_clone = copy_work(work);

	work_clone->clone = true;
	cgtime((struct timeval *)&(work_clone->tv_cloned));
	work_clone->longpoll = false;
	work_clone->mandatory = false;
	/* Make cloned work appear slightly older to bias towards keeping the
	 * master work item which can be further rolled */
	work_clone->tv_staged.tv_sec -= 1;

	return work_clone;
}

static void stage_work(struct work *work);

static bool clone_available(void)
{
	struct work *work_clone = NULL, *work, *tmp;
	bool cloned = false;

	mutex_lock(stgd_lock);
	if (!staged_rollable)
		goto out_unlock;

	HASH_ITER(hh, staged_work, work, tmp) {
		if (can_roll(work) && should_roll(work)) {
			roll_work(work);
			work_clone = make_clone(work);
			roll_work(work);
			cloned = true;
			break;
		}
	}

out_unlock:
	mutex_unlock(stgd_lock);

	if (cloned) {
		applog(LOG_DEBUG, "Pushing cloned available work to stage thread");
		stage_work(work_clone);
	}
	return cloned;
}

static void pool_died(struct pool *pool)
{
	if (!pool_tset(pool, &pool->idle)) {
		cgtime(&pool->tv_idle);
		if (pool == current_pool()) {
			applog(LOG_WARNING, "Pool %d %s not responding!", pool->pool_no, pool->rpc_url);
			switch_pools(NULL);
		} else
			applog(LOG_INFO, "Pool %d %s failed to return work", pool->pool_no, pool->rpc_url);
	}
}

static bool stale_work(struct work *work, bool share)
{
	struct timeval now;
	time_t work_expiry;
	struct pool *pool;
	int getwork_delay;

	if (opt_benchmark)
		return false;

	if (work->work_block != work_block) {
		applog(LOG_DEBUG, "Work stale due to block mismatch");
		return true;
	}

	/* Technically the rolltime should be correct but some pools
	 * advertise a broken expire= that is lower than a meaningful
	 * scantime */
	if (work->rolltime > opt_scantime)
		work_expiry = work->rolltime;
	else
		work_expiry = opt_expiry;

	pool = work->pool;

	if (!share && pool->has_stratum) {
		bool same_job;

		if (!pool->stratum_active || !pool->stratum_notify) {
			applog(LOG_DEBUG, "Work stale due to stratum inactive");
			return true;
		}

		same_job = true;

		cg_rlock(&pool->data_lock);
		if (strcmp(work->job_id, pool->swork.job_id))
			same_job = false;
		cg_runlock(&pool->data_lock);

		if (!same_job) {
			applog(LOG_DEBUG, "Work stale due to stratum job_id mismatch");
			return true;
		}
	}

	/* Factor in the average getwork delay of this pool, rounding it up to
	 * the nearest second */
	getwork_delay = pool->cgminer_pool_stats.getwork_wait_rolling * 5 + 1;
	work_expiry -= getwork_delay;
	if (unlikely(work_expiry < 5))
		work_expiry = 5;

	cgtime(&now);
	if ((now.tv_sec - work->tv_staged.tv_sec) >= work_expiry) {
		applog(LOG_DEBUG, "Work stale due to expiry");
		return true;
	}

	if (opt_fail_only && !share && pool != current_pool() && !work->mandatory &&
	    pool_strategy != POOL_LOADBALANCE && pool_strategy != POOL_BALANCE) {
		applog(LOG_DEBUG, "Work stale due to fail only pool mismatch");
		return true;
	}

	return false;
}

static uint64_t share_diff(const struct work *work)
{
	uint64_t *data64, d64, ret;
	bool new_best = false;
	char rhash[32];

	swab256(rhash, work->hash);
	if (opt_scrypt)
		data64 = (uint64_t *)(rhash + 2);
	else
		data64 = (uint64_t *)(rhash + 4);
	d64 = be64toh(*data64);
	if (unlikely(!d64))
		d64 = 1;
	ret = diffone / d64;

	cg_wlock(&control_lock);
	if (unlikely(ret > best_diff)) {
		new_best = true;
		best_diff = ret;
		suffix_string(best_diff, best_share, 0);
	}
	if (unlikely(ret > work->pool->best_diff))
		work->pool->best_diff = ret;
	cg_wunlock(&control_lock);

	if (unlikely(new_best))
		applog(LOG_INFO, "New best share: %s", best_share);

	return ret;
}

static void regen_hash(struct work *work)
{
	uint32_t *data32 = (uint32_t *)(work->data);
	unsigned char swap[80];
	uint32_t *swap32 = (uint32_t *)swap;
	unsigned char hash1[32];

	flip80(swap32, data32);
	sha2(swap, 80, hash1);
	sha2(hash1, 32, (unsigned char *)(work->hash));
}

static void rebuild_hash(struct work *work)
{
	if (opt_scrypt)
		scrypt_regenhash(work);
	else
		regen_hash(work);

	work->share_diff = share_diff(work);
	if (unlikely(work->share_diff >= current_diff)) {
		work->block = true;
		work->pool->solved++;
		found_blocks++;
		work->mandatory = true;
		applog(LOG_NOTICE, "Found block for pool %d!", work->pool->pool_no);
	}
}

static bool cnx_needed(struct pool *pool);

static void *submit_work_thread(void *userdata)
{
	struct work *work = (struct work *)userdata;
	struct pool *pool = work->pool;
	bool resubmit = false;
	struct curl_ent *ce;

	pthread_detach(pthread_self());

	RenameThread("submit_work");

	applog(LOG_DEBUG, "Creating extra submit work thread");

	ce = pop_curl_entry(pool);
	/* submit solution to bitcoin via JSON-RPC */
	while (!submit_upstream_work(work, ce->curl, resubmit)) {
		if (opt_lowmem) {
			applog(LOG_NOTICE, "Pool %d share being discarded to minimise memory cache", pool->pool_no);
			break;
		}
		resubmit = true;
		if (stale_work(work, true)) {
			applog(LOG_NOTICE, "Pool %d share became stale while retrying submit, discarding", pool->pool_no);

			mutex_lock(&stats_lock);
			total_stale++;
			pool->stale_shares++;
			total_diff_stale += work->work_difficulty;
			pool->diff_stale += work->work_difficulty;
			mutex_unlock(&stats_lock);

			free_work(work);
			break;
		}

		/* pause, then restart work-request loop */
		applog(LOG_INFO, "json_rpc_call failed on submit_work, retrying");
	}
	push_curl_entry(ce, pool);

	return NULL;
}

/* Find the pool that currently has the highest priority */
static struct pool *priority_pool(int choice)
{
	struct pool *ret = NULL;
	int i;

	for (i = 0; i < total_pools; i++) {
		struct pool *pool = pools[i];

		if (pool->prio == choice) {
			ret = pool;
			break;
		}
	}

	if (unlikely(!ret)) {
		applog(LOG_ERR, "WTF No pool %d found!", choice);
		return pools[choice];
	}
	return ret;
}

static void clear_pool_work(struct pool *pool);

/* Specifies whether we can switch to this pool or not. */
static bool pool_unusable(struct pool *pool)
{
	if (pool->idle)
		return true;
	if (pool->enabled != POOL_ENABLED)
		return true;
	return false;
}

void switch_pools(struct pool *selected)
{
	struct pool *pool, *last_pool;
	int i, pool_no, next_pool;

	cg_wlock(&control_lock);
	last_pool = currentpool;
	pool_no = currentpool->pool_no;

	/* Switch selected to pool number 0 and move the rest down */
	if (selected) {
		if (selected->prio != 0) {
			for (i = 0; i < total_pools; i++) {
				pool = pools[i];
				if (pool->prio < selected->prio)
					pool->prio++;
			}
			selected->prio = 0;
		}
	}

	switch (pool_strategy) {
		/* Both of these set to the master pool */
		case POOL_BALANCE:
		case POOL_FAILOVER:
		case POOL_LOADBALANCE:
			for (i = 0; i < total_pools; i++) {
				pool = priority_pool(i);
				if (pool_unusable(pool))
					continue;
				pool_no = pool->pool_no;
				break;
			}
			break;
		/* Both of these simply increment and cycle */
		case POOL_ROUNDROBIN:
		case POOL_ROTATE:
			if (selected && !selected->idle) {
				pool_no = selected->pool_no;
				break;
			}
			next_pool = pool_no;
			/* Select the next alive pool */
			for (i = 1; i < total_pools; i++) {
				next_pool++;
				if (next_pool >= total_pools)
					next_pool = 0;
				pool = pools[next_pool];
				if (pool_unusable(pool))
					continue;
				pool_no = next_pool;
				break;
			}
			break;
		default:
			break;
	}

	currentpool = pools[pool_no];
	pool = currentpool;
	cg_wunlock(&control_lock);

	/* Set the lagging flag to avoid pool not providing work fast enough
	 * messages in failover only mode since  we have to get all fresh work
	 * as in restart_threads */
	if (opt_fail_only)
		pool_tset(pool, &pool->lagging);

	if (pool != last_pool && pool_strategy != POOL_LOADBALANCE && pool_strategy != POOL_BALANCE) {
		applog(LOG_WARNING, "Switching to pool %d %s", pool->pool_no, pool->rpc_url);
		if (pool_localgen(pool) || opt_fail_only)
			clear_pool_work(last_pool);
	}

	mutex_lock(&lp_lock);
	pthread_cond_broadcast(&lp_cond);
	mutex_unlock(&lp_lock);

}

void discard_work(struct work *work)
{
	if (!work->clone && !work->rolls && !work->mined) {
		if (work->pool)
			work->pool->discarded_work++;
		total_discarded++;
		applog(LOG_DEBUG, "Discarded work");
	} else
		applog(LOG_DEBUG, "Discarded cloned or rolled work");
	free_work(work);
}

static void wake_gws(void)
{
	mutex_lock(stgd_lock);
	pthread_cond_signal(&gws_cond);
	mutex_unlock(stgd_lock);
}

static void discard_stale(void)
{
	struct work *work, *tmp;
	int stale = 0;

	mutex_lock(stgd_lock);
	HASH_ITER(hh, staged_work, work, tmp) {
		if (stale_work(work, false)) {
			HASH_DEL(staged_work, work);
			discard_work(work);
			stale++;
		}
	}
	pthread_cond_signal(&gws_cond);
	mutex_unlock(stgd_lock);

	if (stale)
		applog(LOG_DEBUG, "Discarded %d stales that didn't match current hash", stale);
}

/* A generic wait function for threads that poll that will wait a specified
 * time tdiff waiting on the pthread conditional that is broadcast when a
 * work restart is required. Returns the value of pthread_cond_timedwait
 * which is zero if the condition was met or ETIMEDOUT if not.
 */
int restart_wait(unsigned int mstime)
{
	struct timeval now, then, tdiff;
	struct timespec abstime;
	int rc;

	tdiff.tv_sec = mstime / 1000;
	tdiff.tv_usec = mstime * 1000 - (tdiff.tv_sec * 1000000);
	cgtime(&now);
	timeradd(&now, &tdiff, &then);
	abstime.tv_sec = then.tv_sec;
	abstime.tv_nsec = then.tv_usec * 1000;

	mutex_lock(&restart_lock);
	rc = pthread_cond_timedwait(&restart_cond, &restart_lock, &abstime);
	mutex_unlock(&restart_lock);

	return rc;
}
	
static void restart_threads(void)
{
	struct pool *cp = current_pool();
	int i;

	/* Artificially set the lagging flag to avoid pool not providing work
	 * fast enough  messages after every long poll */
	pool_tset(cp, &cp->lagging);

	/* Discard staged work that is now stale */
	discard_stale();

	rd_lock(&mining_thr_lock);
	for (i = 0; i < mining_threads; i++)
		mining_thr[i]->work_restart = true;
	rd_unlock(&mining_thr_lock);

	mutex_lock(&restart_lock);
	pthread_cond_broadcast(&restart_cond);
	mutex_unlock(&restart_lock);
}

static void set_curblock(char *hexstr, unsigned char *hash)
{
	unsigned char hash_swap[32];
	unsigned char block_hash_swap[32];

	strcpy(current_block, hexstr);
	swap256(hash_swap, hash);
	swap256(block_hash_swap, hash + 4);

	cg_wlock(&ch_lock);
	cgtime(&block_timeval);
	free(current_hash);
	current_hash = bin2hex(hash_swap + 2, 8);
	free(current_fullhash);
	current_fullhash = bin2hex(block_hash_swap, 32);
	get_timestamp(blocktime, &block_timeval);
	cg_wunlock(&ch_lock);

	applog(LOG_INFO, "New block: %s... diff %s", current_hash, block_diff);
}

/* Search to see if this string is from a block that has been seen before */
static bool block_exists(char *hexstr)
{
	struct block *s;

	rd_lock(&blk_lock);
	HASH_FIND_STR(blocks, hexstr, s);
	rd_unlock(&blk_lock);

	if (s)
		return true;
	return false;
}

/* Tests if this work is from a block that has been seen before */
static inline bool from_existing_block(struct work *work)
{
	char *hexstr = bin2hex(work->data + 8, 18);
	bool ret;

	ret = block_exists(hexstr);
	free(hexstr);
	return ret;
}

static int block_sort(struct block *blocka, struct block *blockb)
{
	return blocka->block_no - blockb->block_no;
}

static void set_blockdiff(const struct work *work)
{
	uint64_t *data64, d64, diff64;
	double previous_diff;
	uint32_t diffhash[8];
	uint32_t difficulty;
	uint32_t diffbytes;
	uint32_t diffvalue;
	char rhash[32];
	int diffshift;

	difficulty = swab32(*((uint32_t *)(work->data + 72)));

	diffbytes = ((difficulty >> 24) & 0xff) - 3;
	diffvalue = difficulty & 0x00ffffff;

	diffshift = (diffbytes % 4) * 8;
	if (diffshift == 0) {
		diffshift = 32;
		diffbytes--;
	}

	memset(diffhash, 0, 32);
	diffbytes >>= 2;
	if (unlikely(diffbytes > 6))
		return;
	diffhash[diffbytes + 1] = diffvalue >> (32 - diffshift);
	diffhash[diffbytes] = diffvalue << diffshift;

	swab256(rhash, diffhash);

	if (opt_scrypt)
		data64 = (uint64_t *)(rhash + 2);
	else
		data64 = (uint64_t *)(rhash + 4);
	d64 = bswap_64(*data64);
	if (unlikely(!d64))
		d64 = 1;

	previous_diff = current_diff;
	diff64 = diffone / d64;
	suffix_string(diff64, block_diff, 0);
	current_diff = (double)diffone / (double)d64;
	if (unlikely(current_diff != previous_diff))
		applog(LOG_NOTICE, "Network diff set to %s", block_diff);
}

static bool test_work_current(struct work *work)
{
	bool ret = true;
	char *hexstr;

	if (work->mandatory)
		return ret;

	/* Hack to work around dud work sneaking into test */
	hexstr = bin2hex(work->data + 8, 18);
	if (!strncmp(hexstr, "000000000000000000000000000000000000", 36))
		goto out_free;

	/* Search to see if this block exists yet and if not, consider it a
	 * new block and set the current block details to this one */
	if (!block_exists(hexstr)) {
		struct block *s = calloc(sizeof(struct block), 1);
		int deleted_block = 0;
		ret = false;

		if (unlikely(!s))
			quit (1, "test_work_current OOM");
		strcpy(s->hash, hexstr);
		s->block_no = new_blocks++;

		wr_lock(&blk_lock);
		/* Only keep the last hour's worth of blocks in memory since
		 * work from blocks before this is virtually impossible and we
		 * want to prevent memory usage from continually rising */
		if (HASH_COUNT(blocks) > 6) {
			struct block *oldblock;

			HASH_SORT(blocks, block_sort);
			oldblock = blocks;
			deleted_block = oldblock->block_no;
			HASH_DEL(blocks, oldblock);
			free(oldblock);
		}
		HASH_ADD_STR(blocks, hash, s);
		set_blockdiff(work);
		wr_unlock(&blk_lock);

		if (deleted_block)
			applog(LOG_DEBUG, "Deleted block %d from database", deleted_block);
		set_curblock(hexstr, work->data);
		if (unlikely(new_blocks == 1))
			goto out_free;

		work->work_block = ++work_block;

		if (!work->stratum) {
			if (work->longpoll) {
				applog(LOG_NOTICE, "%sLONGPOLL from pool %d detected new block",
				       work->gbt ? "GBT " : "", work->pool->pool_no);
			} else if (have_longpoll)
				applog(LOG_NOTICE, "New block detected on network before longpoll");
			else
				applog(LOG_NOTICE, "New block detected on network");
		}
		restart_threads();
	} else if (work->longpoll) {
		work->work_block = ++work_block;
		if (work->pool == current_pool()) {
			applog(LOG_NOTICE, "%sLONGPOLL from pool %d requested work restart",
			       work->gbt ? "GBT " : "", work->pool->pool_no);
			restart_threads();
		}
	}
	work->longpoll = false;
out_free:
	free(hexstr);
	return ret;
}

static int tv_sort(struct work *worka, struct work *workb)
{
	return worka->tv_staged.tv_sec - workb->tv_staged.tv_sec;
}

static bool work_rollable(struct work *work)
{
	return (!work->clone && work->rolltime);
}

static bool hash_push(struct work *work)
{
	bool rc = true;

	mutex_lock(stgd_lock);
	if (work_rollable(work))
		staged_rollable++;
	if (likely(!getq->frozen)) {
		HASH_ADD_INT(staged_work, id, work);
		HASH_SORT(staged_work, tv_sort);
	} else
		rc = false;
	pthread_cond_broadcast(&getq->cond);
	mutex_unlock(stgd_lock);

	return rc;
}

static void *stage_thread(void *userdata)
{
	struct thr_info *mythr = userdata;
	bool ok = true;

	pthread_setcanceltype(PTHREAD_CANCEL_ASYNCHRONOUS, NULL);

	RenameThread("stage");

	while (ok) {
		struct work *work = NULL;

		applog(LOG_DEBUG, "Popping work to stage thread");

		work = tq_pop(mythr->q, NULL);
		if (unlikely(!work)) {
			applog(LOG_ERR, "Failed to tq_pop in stage_thread");
			ok = false;
			break;
		}
		work->work_block = work_block;

		test_work_current(work);

		applog(LOG_DEBUG, "Pushing work to getwork queue");

		if (unlikely(!hash_push(work))) {
			applog(LOG_WARNING, "Failed to hash_push in stage_thread");
			continue;
		}
	}

	tq_freeze(mythr->q);
	return NULL;
}

static void stage_work(struct work *work)
{
	applog(LOG_DEBUG, "Pushing work from pool %d to hash queue", work->pool->pool_no);
	work->work_block = work_block;
	test_work_current(work);
	hash_push(work);
}

#ifdef HAVE_CURSES
int curses_int(const char *query)
{
	int ret;
	char *cvar;

	cvar = curses_input(query);
	ret = atoi(cvar);
	free(cvar);
	return ret;
}
#endif

#ifdef HAVE_CURSES
static bool input_pool(bool live);
#endif

#ifdef HAVE_CURSES
static void display_pool_summary(struct pool *pool)
{
	double efficiency = 0.0;

	if (curses_active_locked()) {
		wlog("Pool: %s\n", pool->rpc_url);
		if (pool->solved)
			wlog("SOLVED %d BLOCK%s!\n", pool->solved, pool->solved > 1 ? "S" : "");
		wlog("%s own long-poll support\n", pool->hdr_path ? "Has" : "Does not have");
		wlog(" Queued work requests: %d\n", pool->getwork_requested);
		wlog(" Share submissions: %d\n", pool->accepted + pool->rejected);
		wlog(" Accepted shares: %d\n", pool->accepted);
		wlog(" Rejected shares: %d\n", pool->rejected);
		wlog(" Accepted difficulty shares: %1.f\n", pool->diff_accepted);
		wlog(" Rejected difficulty shares: %1.f\n", pool->diff_rejected);
		if (pool->accepted || pool->rejected)
			wlog(" Reject ratio: %.1f%%\n", (double)(pool->rejected * 100) / (double)(pool->accepted + pool->rejected));
		efficiency = pool->getwork_requested ? pool->accepted * 100.0 / pool->getwork_requested : 0.0;
		if (!pool_localgen(pool))
			wlog(" Efficiency (accepted / queued): %.0f%%\n", efficiency);

		wlog(" Discarded work due to new blocks: %d\n", pool->discarded_work);
		wlog(" Stale submissions discarded due to new blocks: %d\n", pool->stale_shares);
		wlog(" Unable to get work from server occasions: %d\n", pool->getfail_occasions);
		wlog(" Submitting work remotely delay occasions: %d\n\n", pool->remotefail_occasions);
		unlock_curses();
	}
}
#endif

/* We can't remove the memory used for this struct pool because there may
 * still be work referencing it. We just remove it from the pools list */
void remove_pool(struct pool *pool)
{
	int i, last_pool = total_pools - 1;
	struct pool *other;

	/* Boost priority of any lower prio than this one */
	for (i = 0; i < total_pools; i++) {
		other = pools[i];
		if (other->prio > pool->prio)
			other->prio--;
	}

	if (pool->pool_no < last_pool) {
		/* Swap the last pool for this one */
		(pools[last_pool])->pool_no = pool->pool_no;
		pools[pool->pool_no] = pools[last_pool];
	}
	/* Give it an invalid number */
	pool->pool_no = total_pools;
	pool->removed = true;
	total_pools--;
}

/* add a mutex if this needs to be thread safe in the future */
static struct JE {
	char *buf;
	struct JE *next;
} *jedata = NULL;

static void json_escape_free()
{
	struct JE *jeptr = jedata;
	struct JE *jenext;

	jedata = NULL;

	while (jeptr) {
		jenext = jeptr->next;
		free(jeptr->buf);
		free(jeptr);
		jeptr = jenext;
	}
}

static char *json_escape(char *str)
{
	struct JE *jeptr;
	char *buf, *ptr;

	/* 2x is the max, may as well just allocate that */
	ptr = buf = malloc(strlen(str) * 2 + 1);

	jeptr = malloc(sizeof(*jeptr));

	jeptr->buf = buf;
	jeptr->next = jedata;
	jedata = jeptr;

	while (*str) {
		if (*str == '\\' || *str == '"')
			*(ptr++) = '\\';

		*(ptr++) = *(str++);
	}

	*ptr = '\0';

	return buf;
}

void write_config(FILE *fcfg)
{
	int i;

	/* Write pool values */
	fputs("{\n\"pools\" : [", fcfg);
	for(i = 0; i < total_pools; i++) {
		fprintf(fcfg, "%s\n\t{\n\t\t\"url\" : \"%s%s%s%s\",", i > 0 ? "," : "",
			pools[i]->rpc_proxy ? json_escape((char *)proxytype(pools[i]->rpc_proxytype)) : "",
			pools[i]->rpc_proxy ? json_escape(pools[i]->rpc_proxy) : "",
			pools[i]->rpc_proxy ? "|" : "",
			json_escape(pools[i]->rpc_url));
		fprintf(fcfg, "\n\t\t\"user\" : \"%s\",", json_escape(pools[i]->rpc_user));
		fprintf(fcfg, "\n\t\t\"pass\" : \"%s\"\n\t}", json_escape(pools[i]->rpc_pass));
		}
	fputs("\n]\n", fcfg);

#ifdef HAVE_OPENCL
	if (nDevs) {
		/* Write GPU device values */
		fputs(",\n\"intensity\" : \"", fcfg);
		for(i = 0; i < nDevs; i++)
			fprintf(fcfg, gpus[i].dynamic ? "%sd" : "%s%d", i > 0 ? "," : "", gpus[i].intensity);
		fputs("\",\n\"vectors\" : \"", fcfg);
		for(i = 0; i < nDevs; i++)
			fprintf(fcfg, "%s%d", i > 0 ? "," : "",
				gpus[i].vwidth);
		fputs("\",\n\"worksize\" : \"", fcfg);
		for(i = 0; i < nDevs; i++)
			fprintf(fcfg, "%s%d", i > 0 ? "," : "",
				(int)gpus[i].work_size);
		fputs("\",\n\"kernel\" : \"", fcfg);
		for(i = 0; i < nDevs; i++) {
			fprintf(fcfg, "%s", i > 0 ? "," : "");
			switch (gpus[i].kernel) {
				case KL_NONE: // Shouldn't happen
					break;
				case KL_POCLBM:
					fprintf(fcfg, "poclbm");
					break;
				case KL_PHATK:
					fprintf(fcfg, "phatk");
					break;
				case KL_DIAKGCN:
					fprintf(fcfg, "diakgcn");
					break;
				case KL_DIABLO:
					fprintf(fcfg, "diablo");
					break;
				case KL_SCRYPT:
					fprintf(fcfg, "scrypt");
					break;
			}
		}
#ifdef USE_SCRYPT
		fputs("\",\n\"lookup-gap\" : \"", fcfg);
		for(i = 0; i < nDevs; i++)
			fprintf(fcfg, "%s%d", i > 0 ? "," : "",
				(int)gpus[i].opt_lg);
		fputs("\",\n\"thread-concurrency\" : \"", fcfg);
		for(i = 0; i < nDevs; i++)
			fprintf(fcfg, "%s%d", i > 0 ? "," : "",
				(int)gpus[i].opt_tc);
		fputs("\",\n\"shaders\" : \"", fcfg);
		for(i = 0; i < nDevs; i++)
			fprintf(fcfg, "%s%d", i > 0 ? "," : "",
				(int)gpus[i].shaders);
#endif
#ifdef HAVE_ADL
		fputs("\",\n\"gpu-engine\" : \"", fcfg);
		for(i = 0; i < nDevs; i++)
			fprintf(fcfg, "%s%d-%d", i > 0 ? "," : "", gpus[i].min_engine, gpus[i].gpu_engine);
		fputs("\",\n\"gpu-fan\" : \"", fcfg);
		for(i = 0; i < nDevs; i++)
			fprintf(fcfg, "%s%d-%d", i > 0 ? "," : "", gpus[i].min_fan, gpus[i].gpu_fan);
		fputs("\",\n\"gpu-memclock\" : \"", fcfg);
		for(i = 0; i < nDevs; i++)
			fprintf(fcfg, "%s%d", i > 0 ? "," : "", gpus[i].gpu_memclock);
		fputs("\",\n\"gpu-memdiff\" : \"", fcfg);
		for(i = 0; i < nDevs; i++)
			fprintf(fcfg, "%s%d", i > 0 ? "," : "", gpus[i].gpu_memdiff);
		fputs("\",\n\"gpu-powertune\" : \"", fcfg);
		for(i = 0; i < nDevs; i++)
			fprintf(fcfg, "%s%d", i > 0 ? "," : "", gpus[i].gpu_powertune);
		fputs("\",\n\"gpu-vddc\" : \"", fcfg);
		for(i = 0; i < nDevs; i++)
			fprintf(fcfg, "%s%1.3f", i > 0 ? "," : "", gpus[i].gpu_vddc);
		fputs("\",\n\"temp-cutoff\" : \"", fcfg);
		for(i = 0; i < nDevs; i++)
			fprintf(fcfg, "%s%d", i > 0 ? "," : "", gpus[i].cutofftemp);
		fputs("\",\n\"temp-overheat\" : \"", fcfg);
		for(i = 0; i < nDevs; i++)
			fprintf(fcfg, "%s%d", i > 0 ? "," : "", gpus[i].adl.overtemp);
		fputs("\",\n\"temp-target\" : \"", fcfg);
		for(i = 0; i < nDevs; i++)
			fprintf(fcfg, "%s%d", i > 0 ? "," : "", gpus[i].adl.targettemp);
#endif
		fputs("\"", fcfg);
	}
#endif
#ifdef HAVE_ADL
	if (opt_reorder)
		fprintf(fcfg, ",\n\"gpu-reorder\" : true");
#endif

	/* Simple bool and int options */
	struct opt_table *opt;
	for (opt = opt_config_table; opt->type != OPT_END; opt++) {
		char *p, *name = strdup(opt->names);
		for (p = strtok(name, "|"); p; p = strtok(NULL, "|")) {
			if (p[1] != '-')
				continue;
			if (opt->type & OPT_NOARG &&
			   ((void *)opt->cb == (void *)opt_set_bool || (void *)opt->cb == (void *)opt_set_invbool) &&
			   (*(bool *)opt->u.arg == ((void *)opt->cb == (void *)opt_set_bool)))
				fprintf(fcfg, ",\n\"%s\" : true", p+2);

			if (opt->type & OPT_HASARG &&
			   ((void *)opt->cb_arg == (void *)set_int_0_to_9999 ||
			   (void *)opt->cb_arg == (void *)set_int_1_to_65535 ||
			   (void *)opt->cb_arg == (void *)set_int_0_to_10 ||
			   (void *)opt->cb_arg == (void *)set_int_1_to_10) && opt->desc != opt_hidden)
				fprintf(fcfg, ",\n\"%s\" : \"%d\"", p+2, *(int *)opt->u.arg);
		}
	}

	/* Special case options */
	fprintf(fcfg, ",\n\"shares\" : \"%d\"", opt_shares);
	if (pool_strategy == POOL_BALANCE)
		fputs(",\n\"balance\" : true", fcfg);
	if (pool_strategy == POOL_LOADBALANCE)
		fputs(",\n\"load-balance\" : true", fcfg);
	if (pool_strategy == POOL_ROUNDROBIN)
		fputs(",\n\"round-robin\" : true", fcfg);
	if (pool_strategy == POOL_ROTATE)
		fprintf(fcfg, ",\n\"rotate\" : \"%d\"", opt_rotate_period);
#if defined(unix) || defined(__APPLE__)
	if (opt_stderr_cmd && *opt_stderr_cmd)
		fprintf(fcfg, ",\n\"monitor\" : \"%s\"", json_escape(opt_stderr_cmd));
#endif // defined(unix)
	if (opt_kernel_path && *opt_kernel_path) {
		char *kpath = strdup(opt_kernel_path);
		if (kpath[strlen(kpath)-1] == '/')
			kpath[strlen(kpath)-1] = 0;
		fprintf(fcfg, ",\n\"kernel-path\" : \"%s\"", json_escape(kpath));
	}
	if (schedstart.enable)
		fprintf(fcfg, ",\n\"sched-time\" : \"%d:%d\"", schedstart.tm.tm_hour, schedstart.tm.tm_min);
	if (schedstop.enable)
		fprintf(fcfg, ",\n\"stop-time\" : \"%d:%d\"", schedstop.tm.tm_hour, schedstop.tm.tm_min);
	if (opt_socks_proxy && *opt_socks_proxy)
		fprintf(fcfg, ",\n\"socks-proxy\" : \"%s\"", json_escape(opt_socks_proxy));
	if (opt_devs_enabled) {
		fprintf(fcfg, ",\n\"device\" : \"");
		bool extra_devs = false;

		for (i = 0; i < MAX_DEVICES; i++) {
			if (devices_enabled[i]) {
				int startd = i;

				if (extra_devs)
					fprintf(fcfg, ",");
				while (i < MAX_DEVICES && devices_enabled[i + 1])
					++i;
				fprintf(fcfg, "%d", startd);
				if (i > startd)
					fprintf(fcfg, "-%d", i);
			}
		}
		fprintf(fcfg, "\"");
	}
	if (opt_removedisabled)
		fprintf(fcfg, ",\n\"remove-disabled\" : true");
	if (opt_api_allow)
		fprintf(fcfg, ",\n\"api-allow\" : \"%s\"", json_escape(opt_api_allow));
	if (strcmp(opt_api_description, PACKAGE_STRING) != 0)
		fprintf(fcfg, ",\n\"api-description\" : \"%s\"", json_escape(opt_api_description));
	if (opt_api_groups)
		fprintf(fcfg, ",\n\"api-groups\" : \"%s\"", json_escape(opt_api_groups));
	if (opt_icarus_options)
		fprintf(fcfg, ",\n\"icarus-options\" : \"%s\"", json_escape(opt_icarus_options));
	if (opt_icarus_timing)
		fprintf(fcfg, ",\n\"icarus-timing\" : \"%s\"", json_escape(opt_icarus_timing));
	if (opt_klondike_options)
		fprintf(fcfg, ",\n\"klondike-options\" : \"%s\"", json_escape(opt_klondike_options));
#ifdef USE_USBUTILS
	if (opt_usb_select)
		fprintf(fcfg, ",\n\"usb\" : \"%s\"", json_escape(opt_usb_select));
#endif
	fputs("\n}\n", fcfg);

	json_escape_free();
}

void zero_bestshare(void)
{
	int i;

	best_diff = 0;
	memset(best_share, 0, 8);
	suffix_string(best_diff, best_share, 0);

	for (i = 0; i < total_pools; i++) {
		struct pool *pool = pools[i];
		pool->best_diff = 0;
	}
}

void zero_stats(void)
{
	int i;

	cgtime(&total_tv_start);
	total_mhashes_done = 0;
	total_getworks = 0;
	total_accepted = 0;
	total_rejected = 0;
	hw_errors = 0;
	total_stale = 0;
	total_discarded = 0;
	local_work = 0;
	total_go = 0;
	total_ro = 0;
	total_secs = 1.0;
	total_diff1 = 0;
	found_blocks = 0;
	total_diff_accepted = 0;
	total_diff_rejected = 0;
	total_diff_stale = 0;

	for (i = 0; i < total_pools; i++) {
		struct pool *pool = pools[i];

		pool->getwork_requested = 0;
		pool->accepted = 0;
		pool->rejected = 0;
		pool->stale_shares = 0;
		pool->discarded_work = 0;
		pool->getfail_occasions = 0;
		pool->remotefail_occasions = 0;
		pool->last_share_time = 0;
		pool->diff1 = 0;
		pool->diff_accepted = 0;
		pool->diff_rejected = 0;
		pool->diff_stale = 0;
		pool->last_share_diff = 0;
	}

	zero_bestshare();

	for (i = 0; i < total_devices; ++i) {
		struct cgpu_info *cgpu = get_devices(i);

		mutex_lock(&hash_lock);
		cgpu->total_mhashes = 0;
		cgpu->accepted = 0;
		cgpu->rejected = 0;
		cgpu->hw_errors = 0;
		cgpu->utility = 0.0;
		cgpu->last_share_pool_time = 0;
		cgpu->diff1 = 0;
		cgpu->diff_accepted = 0;
		cgpu->diff_rejected = 0;
		cgpu->last_share_diff = 0;
		mutex_unlock(&hash_lock);
	}
}

#ifdef HAVE_CURSES
static void display_pools(void)
{
	struct pool *pool;
	int selected, i;
	char input;

	opt_loginput = true;
	immedok(logwin, true);
	clear_logwin();
updated:
	for (i = 0; i < total_pools; i++) {
		pool = pools[i];

		if (pool == current_pool())
			wattron(logwin, A_BOLD);
		if (pool->enabled != POOL_ENABLED)
			wattron(logwin, A_DIM);
		wlogprint("%d: ", pool->pool_no);
		switch (pool->enabled) {
			case POOL_ENABLED:
				wlogprint("Enabled ");
				break;
			case POOL_DISABLED:
				wlogprint("Disabled ");
				break;
			case POOL_REJECTING:
				wlogprint("Rejecting ");
				break;
		}
		wlogprint("%s Priority %d: %s  User:%s\n",
			pool->idle? "Dead" : "Alive",
			pool->prio,
			pool->rpc_url, pool->rpc_user);
		wattroff(logwin, A_BOLD | A_DIM);
	}
retry:
	wlogprint("\nCurrent pool management strategy: %s\n",
		strategies[pool_strategy].s);
	if (pool_strategy == POOL_ROTATE)
		wlogprint("Set to rotate every %d minutes\n", opt_rotate_period);
	wlogprint("[F]ailover only %s\n", opt_fail_only ? "enabled" : "disabled");
	wlogprint("[A]dd pool [R]emove pool [D]isable pool [E]nable pool\n");
	wlogprint("[C]hange management strategy [S]witch pool [I]nformation\n");
	wlogprint("Or press any other key to continue\n");
	logwin_update();
	input = getch();

	if (!strncasecmp(&input, "a", 1)) {
		input_pool(true);
		goto updated;
	} else if (!strncasecmp(&input, "r", 1)) {
		if (total_pools <= 1) {
			wlogprint("Cannot remove last pool");
			goto retry;
		}
		selected = curses_int("Select pool number");
		if (selected < 0 || selected >= total_pools) {
			wlogprint("Invalid selection\n");
			goto retry;
		}
		pool = pools[selected];
		if (pool == current_pool())
			switch_pools(NULL);
		if (pool == current_pool()) {
			wlogprint("Unable to remove pool due to activity\n");
			goto retry;
		}
		disable_pool(pool);
		remove_pool(pool);
		goto updated;
	} else if (!strncasecmp(&input, "s", 1)) {
		selected = curses_int("Select pool number");
		if (selected < 0 || selected >= total_pools) {
			wlogprint("Invalid selection\n");
			goto retry;
		}
		pool = pools[selected];
		enable_pool(pool);
		switch_pools(pool);
		goto updated;
	} else if (!strncasecmp(&input, "d", 1)) {
		if (enabled_pools <= 1) {
			wlogprint("Cannot disable last pool");
			goto retry;
		}
		selected = curses_int("Select pool number");
		if (selected < 0 || selected >= total_pools) {
			wlogprint("Invalid selection\n");
			goto retry;
		}
		pool = pools[selected];
		disable_pool(pool);
		if (pool == current_pool())
			switch_pools(NULL);
		goto updated;
	} else if (!strncasecmp(&input, "e", 1)) {
		selected = curses_int("Select pool number");
		if (selected < 0 || selected >= total_pools) {
			wlogprint("Invalid selection\n");
			goto retry;
		}
		pool = pools[selected];
		enable_pool(pool);
		if (pool->prio < current_pool()->prio)
			switch_pools(pool);
		goto updated;
	} else if (!strncasecmp(&input, "c", 1)) {
		for (i = 0; i <= TOP_STRATEGY; i++)
			wlogprint("%d: %s\n", i, strategies[i].s);
		selected = curses_int("Select strategy number type");
		if (selected < 0 || selected > TOP_STRATEGY) {
			wlogprint("Invalid selection\n");
			goto retry;
		}
		if (selected == POOL_ROTATE) {
			opt_rotate_period = curses_int("Select interval in minutes");

			if (opt_rotate_period < 0 || opt_rotate_period > 9999) {
				opt_rotate_period = 0;
				wlogprint("Invalid selection\n");
				goto retry;
			}
		}
		pool_strategy = selected;
		switch_pools(NULL);
		goto updated;
	} else if (!strncasecmp(&input, "i", 1)) {
		selected = curses_int("Select pool number");
		if (selected < 0 || selected >= total_pools) {
			wlogprint("Invalid selection\n");
			goto retry;
		}
		pool = pools[selected];
		display_pool_summary(pool);
		goto retry;
	} else if (!strncasecmp(&input, "f", 1)) {
		opt_fail_only ^= true;
		goto updated;
	} else
		clear_logwin();

	immedok(logwin, false);
	opt_loginput = false;
}

static void display_options(void)
{
	int selected;
	char input;

	opt_loginput = true;
	immedok(logwin, true);
	clear_logwin();
retry:
	wlogprint("[N]ormal [C]lear [S]ilent mode (disable all output)\n");
	wlogprint("[D]ebug:%s\n[P]er-device:%s\n[Q]uiet:%s\n[V]erbose:%s\n"
		  "[R]PC debug:%s\n[W]orkTime details:%s\nco[M]pact: %s\n"
		  "[L]og interval:%d\n[Z]ero statistics\n",
		opt_debug ? "on" : "off",
	        want_per_device_stats? "on" : "off",
		opt_quiet ? "on" : "off",
		opt_log_output ? "on" : "off",
		opt_protocol ? "on" : "off",
		opt_worktime ? "on" : "off",
		opt_compact ? "on" : "off",
		opt_log_interval);
	wlogprint("Select an option or any other key to return\n");
	logwin_update();
	input = getch();
	if (!strncasecmp(&input, "q", 1)) {
		opt_quiet ^= true;
		wlogprint("Quiet mode %s\n", opt_quiet ? "enabled" : "disabled");
		goto retry;
	} else if (!strncasecmp(&input, "v", 1)) {
		opt_log_output ^= true;
		if (opt_log_output)
			opt_quiet = false;
		wlogprint("Verbose mode %s\n", opt_log_output ? "enabled" : "disabled");
		goto retry;
	} else if (!strncasecmp(&input, "n", 1)) {
		opt_log_output = false;
		opt_debug = false;
		opt_quiet = false;
		opt_protocol = false;
		opt_compact = false;
		want_per_device_stats = false;
		wlogprint("Output mode reset to normal\n");
		switch_logsize();
		goto retry;
	} else if (!strncasecmp(&input, "d", 1)) {
		opt_debug ^= true;
		opt_log_output = opt_debug;
		if (opt_debug)
			opt_quiet = false;
		wlogprint("Debug mode %s\n", opt_debug ? "enabled" : "disabled");
		goto retry;
	} else if (!strncasecmp(&input, "m", 1)) {
		opt_compact ^= true;
		wlogprint("Compact mode %s\n", opt_compact ? "enabled" : "disabled");
		switch_logsize();
		goto retry;
	} else if (!strncasecmp(&input, "p", 1)) {
		want_per_device_stats ^= true;
		opt_log_output = want_per_device_stats;
		wlogprint("Per-device stats %s\n", want_per_device_stats ? "enabled" : "disabled");
		goto retry;
	} else if (!strncasecmp(&input, "r", 1)) {
		opt_protocol ^= true;
		if (opt_protocol)
			opt_quiet = false;
		wlogprint("RPC protocol debugging %s\n", opt_protocol ? "enabled" : "disabled");
		goto retry;
	} else if (!strncasecmp(&input, "c", 1))
		clear_logwin();
	else if (!strncasecmp(&input, "l", 1)) {
		selected = curses_int("Interval in seconds");
		if (selected < 0 || selected > 9999) {
			wlogprint("Invalid selection\n");
			goto retry;
		}
		opt_log_interval = selected;
		wlogprint("Log interval set to %d seconds\n", opt_log_interval);
		goto retry;
	} else if (!strncasecmp(&input, "s", 1)) {
		opt_realquiet = true;
	} else if (!strncasecmp(&input, "w", 1)) {
		opt_worktime ^= true;
		wlogprint("WorkTime details %s\n", opt_worktime ? "enabled" : "disabled");
		goto retry;
	} else if (!strncasecmp(&input, "z", 1)) {
		zero_stats();
		goto retry;
	} else
		clear_logwin();

	immedok(logwin, false);
	opt_loginput = false;
}
#endif

void default_save_file(char *filename)
{
	if (default_config && *default_config) {
		strcpy(filename, default_config);
		return;
	}

#if defined(unix) || defined(__APPLE__)
	if (getenv("HOME") && *getenv("HOME")) {
	        strcpy(filename, getenv("HOME"));
		strcat(filename, "/");
	}
	else
		strcpy(filename, "");
	strcat(filename, ".cgminer/");
	mkdir(filename, 0777);
#else
	strcpy(filename, "");
#endif
	strcat(filename, def_conf);
}

#ifdef HAVE_CURSES
static void set_options(void)
{
	int selected;
	char input;

	opt_loginput = true;
	immedok(logwin, true);
	clear_logwin();
retry:
	wlogprint("[Q]ueue: %d\n[S]cantime: %d\n[E]xpiry: %d\n"
		  "[W]rite config file\n[C]gminer restart\n",
		opt_queue, opt_scantime, opt_expiry);
	wlogprint("Select an option or any other key to return\n");
	logwin_update();
	input = getch();

	if (!strncasecmp(&input, "q", 1)) {
		selected = curses_int("Extra work items to queue");
		if (selected < 0 || selected > 9999) {
			wlogprint("Invalid selection\n");
			goto retry;
		}
		opt_queue = selected;
		goto retry;
	} else if  (!strncasecmp(&input, "s", 1)) {
		selected = curses_int("Set scantime in seconds");
		if (selected < 0 || selected > 9999) {
			wlogprint("Invalid selection\n");
			goto retry;
		}
		opt_scantime = selected;
		goto retry;
	} else if  (!strncasecmp(&input, "e", 1)) {
		selected = curses_int("Set expiry time in seconds");
		if (selected < 0 || selected > 9999) {
			wlogprint("Invalid selection\n");
			goto retry;
		}
		opt_expiry = selected;
		goto retry;
	} else if  (!strncasecmp(&input, "w", 1)) {
		FILE *fcfg;
		char *str, filename[PATH_MAX], prompt[PATH_MAX + 50];

		default_save_file(filename);
		sprintf(prompt, "Config filename to write (Enter for default) [%s]", filename);
		str = curses_input(prompt);
		if (strcmp(str, "-1")) {
			struct stat statbuf;

			strcpy(filename, str);
			free(str);
			if (!stat(filename, &statbuf)) {
				wlogprint("File exists, overwrite?\n");
				input = getch();
				if (strncasecmp(&input, "y", 1))
					goto retry;
			}
		}
		else
			free(str);
		fcfg = fopen(filename, "w");
		if (!fcfg) {
			wlogprint("Cannot open or create file\n");
			goto retry;
		}
		write_config(fcfg);
		fclose(fcfg);
		goto retry;

	} else if (!strncasecmp(&input, "c", 1)) {
		wlogprint("Are you sure?\n");
		input = getch();
		if (!strncasecmp(&input, "y", 1))
			app_restart();
		else
			clear_logwin();
	} else
		clear_logwin();

	immedok(logwin, false);
	opt_loginput = false;
}

static void *input_thread(void __maybe_unused *userdata)
{
	pthread_setcanceltype(PTHREAD_CANCEL_ASYNCHRONOUS, NULL);

	RenameThread("input");

	if (!curses_active)
		return NULL;

	while (1) {
		char input;

		input = getch();
		if (!strncasecmp(&input, "q", 1)) {
			kill_work();
			return NULL;
		} else if (!strncasecmp(&input, "d", 1))
			display_options();
		else if (!strncasecmp(&input, "p", 1))
			display_pools();
		else if (!strncasecmp(&input, "s", 1))
			set_options();
		else if (have_opencl && !strncasecmp(&input, "g", 1))
			manage_gpu();
		if (opt_realquiet) {
			disable_curses();
			break;
		}
	}

	return NULL;
}
#endif

static void *api_thread(void *userdata)
{
	struct thr_info *mythr = userdata;

	pthread_detach(pthread_self());
	pthread_setcanceltype(PTHREAD_CANCEL_ASYNCHRONOUS, NULL);

	RenameThread("api");

	api(api_thr_id);

	PTH(mythr) = 0L;

	return NULL;
}
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
